JakubSperka/geometeo_logger/calibration_sample/etalon_calibration_sample.csv

 | P, hPa | T, °C | RH, %
3.8.2026 8:03:03 | 996.65 | 35.93 | 29.54
3.8.2026 8:04:03 | 996.68 | 35.96 | 29.65
3.8.2026 8:05:03 | 996.66 | 36.00 | 29.68
3.8.2026 8:06:03 | 996.71 | 36.05 | 29.63
3.8.2026 8:07:03 | 996.69 | 36.09 | 29.60
3.8.2026 8:08:03 | 996.72 | 36.15 | 29.39
3.8.2026 8:09:03 | 996.74 | 36.19 | 29.29
3.8.2026 8:10:03 | 996.74 | 36.33 | 29.07
3.8.2026 8:11:03 | 996.75 | 36.48 | 28.80
3.8.2026 8:12:03 | 996.76 | 36.61 | 28.59
3.8.2026 8:13:03 | 996.78 | 36.68 | 28.42
3.8.2026 8:14:03 | 996.76 | 36.77 | 28.29
3.8.2026 8:15:03 | 996.76 | 36.85 | 28.14
3.8.2026 8:16:03 | 996.76 | 36.92 | 28.05
3.8.2026 8:17:03 | 996.75 | 36.97 | 27.94
3.8.2026 8:18:03 | 996.76 | 37.00 | 27.86
3.8.2026 8:19:03 | 996.77 | 37.04 | 27.78
3.8.2026 8:20:03 | 996.77 | 37.06 | 27.74
3.8.2026 8:21:03 | 996.77 | 37.10 | 27.66
3.8.2026 8:22:03 | 996.75 | 37.13 | 27.60
3.8.2026 8:23:03 | 996.75 | 37.17 | 27.57
3.8.2026 8:24:03 | 996.76 | 37.19 | 27.51
3.8.2026 8:25:03 | 996.76 | 37.23 | 27.44
3.8.2026 8:26:03 | 996.76 | 37.24 | 27.41
3.8.2026 8:27:03 | 996.72 | 37.27 | 27.37
3.8.2026 8:28:03 | 996.72 | 37.32 | 27.31
3.8.2026 8:29:03 | 996.72 | 37.33 | 27.27
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
