JakubSperka/geometeo_logger/calibration_sample/etalon_validation_sample.csv

 | P, hPa | T, °C | RH, %
3.8.2026 13:13:59 | 995.87 | 36.42 | 28.21
3.8.2026 13:14:59 | 995.86 | 36.42 | 29.03
3.8.2026 13:15:59 | 995.84 | 36.50 | 28.40
3.8.2026 13:16:59 | 995.83 | 36.56 | 28.26
3.8.2026 13:17:59 | 995.81 | 36.56 | 28.51
3.8.2026 13:18:59 | 995.78 | 36.58 | 28.78
3.8.2026 13:19:59 | 995.77 | 36.23 | 28.24
3.8.2026 13:20:59 | 995.77 | 35.81 | 28.59
3.8.2026 13:21:59 | 995.77 | 35.21 | 28.88
3.8.2026 13:22:59 | 995.78 | 34.63 | 29.39
3.8.2026 13:23:59 | 995.77 | 34.02 | 30.06
3.8.2026 13:24:59 | 995.74 | 33.63 | 30.46
3.8.2026 13:25:59 | 995.74 | 33.16 | 30.86
3.8.2026 13:26:59 | 995.72 | 32.77 | 31.19
3.8.2026 13:27:59 | 995.71 | 32.50 | 31.57
3.8.2026 13:28:59 | 995.74 | 32.23 | 31.76
3.8.2026 13:29:59 | 995.73 | 31.99 | 31.85
3.8.2026 13:30:59 | 995.73 | 31.78 | 31.99
3.8.2026 13:31:59 | 995.72 | 31.65 | 32.11
3.8.2026 13:32:59 | 995.70 | 31.47 | 32.24
3.8.2026 13:33:59 | 995.67 | 31.28 | 32.26
3.8.2026 13:34:59 | 995.64 | 31.11 | 32.38
3.8.2026 13:35:59 | 995.64 | 31.13 | 32.31
3.8.2026 13:36:59 | 995.62 | 31.00 | 32.33
3.8.2026 13:37:59 | 995.62 | 30.95 | 32.42
3.8.2026 13:38:59 | 995.61 | 30.94 | 32.36
3.8.2026 13:39:59 | 995.59 | 30.90 | 32.43
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
