JakubSperka/geometeo_logger/_stable/geometeo_logger_v0_9_1_stable.ino

#include <Arduino.h>
#include <Wire.h>
#include <SPI.h>
#include <FS.h>
#include <SD.h>
#include <TFT_eSPI.h>

#include "FT6236.h"

#include <Adafruit_SHT4x.h>
#include <Adafruit_BMP280.h>
#include <RTClib.h>
#include <Preferences.h>
#include <WiFi.h>
#include <WebServer.h>
#include <esp_arduino_version.h>
#include <pgmspace.h>

// ============================================================
// GEOMETEO LOGGER - INFORMACIE O FIRMVÉRI
// Pri dalsej verzii staci upravit hodnotu APP_VERSION.
// ============================================================

constexpr char APP_NAME[] = "GEOMETEO LOGGER";
constexpr char APP_VERSION[] = "v0.9.1 (STABLE)";

// ============================================================
// HARDVER: INTERNA I2C ZBERNICA - DOTYK
// ============================================================

constexpr uint8_t INTERNAL_I2C_SDA = 42;
constexpr uint8_t INTERNAL_I2C_SCL = 2;

// ============================================================
// HARDVER: EXTERNA I2C ZBERNICA - METEO SENZOR A RTC
// ============================================================

constexpr uint8_t EXTERNAL_I2C_SDA = 5;
constexpr uint8_t EXTERNAL_I2C_SCL = 6;
constexpr uint32_t I2C_FREQUENCY = 100000;

// ============================================================
// HARDVER: SD KARTA - ESPD-35 v3.2
// ============================================================

constexpr uint8_t SD_SCK_PIN = 14;
constexpr uint8_t SD_MISO_PIN = 21;
constexpr uint8_t SD_MOSI_PIN = 38;
constexpr uint8_t SD_CS_PIN = 17;
constexpr uint32_t SD_SPI_FREQUENCY = 4000000;

// ============================================================
// SENZORY
// ============================================================

constexpr uint8_t BMP280_I2C_ADDRESS = 0x77;

// ============================================================
// BATERIA - ESPD-35 v3.2
// ============================================================

constexpr uint8_t BATTERY_ADC_PIN = 9;
constexpr float BATTERY_DIVIDER_RATIO = 1.7693877551F;
constexpr uint32_t BATTERY_INTERVAL_MS = 5000;
constexpr uint8_t BATTERY_SAMPLE_COUNT = 16;

constexpr uint8_t BATTERY_WARNING_PERCENT = 25;
constexpr uint8_t BATTERY_CRITICAL_PERCENT = 10;

// ============================================================
// SPOĽAHLIVOST A VALIDACIA
// ============================================================

constexpr uint32_t SD_RECOVERY_INTERVAL_MS = 5000;
constexpr uint8_t SD_WRITE_ATTEMPTS = 2;

// Ochrana FAT32 a volneho miesta.
// Jeden FAT32 subor moze mat najviac 4 GiB - 1 B. Relacia sa
// preventivne rozdeli uz pri 3800 MiB, aby zostala bezpecna rezerva.
constexpr uint64_t FAT32_MAX_FILE_SIZE_BYTES = 0xFFFFFFFFULL;

// Pre overenie delenia bez vytvarania viacgigabajtoveho suboru
// mozno docasne nastavit STORAGE_ROTATION_TEST_MODE na true.
// V produkcnej verzii musi zostat false.
constexpr bool STORAGE_ROTATION_TEST_MODE = false;

constexpr uint64_t SESSION_FILE_ROTATE_LIMIT_BYTES =
    STORAGE_ROTATION_TEST_MODE
        ? 64ULL * 1024ULL
        : 3800ULL * 1024ULL * 1024ULL;

constexpr uint64_t SD_LOW_SPACE_WARNING_BYTES =
    32ULL * 1024ULL * 1024ULL;

constexpr uint64_t SD_NORMAL_FREE_RESERVE_BYTES =
    4ULL * 1024ULL * 1024ULL;

constexpr uint64_t SD_EMERGENCY_FREE_RESERVE_BYTES =
    64ULL * 1024ULL;

constexpr uint32_t SD_SPACE_CHECK_INTERVAL_MS = 5000;
constexpr size_t SESSION_FILE_PATH_LENGTH = 112;
constexpr size_t SESSION_MAX_FILE_PARTS = 32;
constexpr size_t CSV_RECORD_ESTIMATE_BYTES = 1024;

static_assert(
    SESSION_FILE_ROTATE_LIMIT_BYTES <
        FAT32_MAX_FILE_SIZE_BYTES,
    "Limit rotacie musi byt mensi ako limit FAT32."
);

constexpr float MIN_VALID_TEMPERATURE_C = -40.0F;
constexpr float MAX_VALID_TEMPERATURE_C = 85.0F;
constexpr float MIN_VALID_HUMIDITY_PERCENT = 0.0F;
constexpr float MAX_VALID_HUMIDITY_PERCENT = 100.0F;
constexpr float MIN_VALID_PRESSURE_HPA = 300.0F;
constexpr float MAX_VALID_PRESSURE_HPA = 1100.0F;

constexpr uint16_t MIN_VALID_RTC_YEAR = 2020;
constexpr uint16_t MAX_VALID_RTC_YEAR = 2099;

// ============================================================
// KALIBRACIA - LINEARNA KOREKCIA y = a*x + b
// Neutralne hodnoty nemenia meranie. Konkretne koeficienty
// sa doplnia po porovnani s laboratornym meradlom.
// ============================================================

constexpr float DEFAULT_CALIBRATION_SCALE = 1.0F;
constexpr float DEFAULT_CALIBRATION_OFFSET = 0.0F;

constexpr float MIN_CALIBRATION_SCALE = 0.5F;
constexpr float MAX_CALIBRATION_SCALE = 1.5F;

constexpr float MIN_TEMPERATURE_OFFSET_C = -20.0F;
constexpr float MAX_TEMPERATURE_OFFSET_C = 20.0F;
constexpr float MIN_HUMIDITY_OFFSET_PERCENT = -50.0F;
constexpr float MAX_HUMIDITY_OFFSET_PERCENT = 50.0F;
constexpr float MIN_PRESSURE_OFFSET_HPA = -150.0F;
constexpr float MAX_PRESSURE_OFFSET_HPA = 150.0F;

// ============================================================
// CASOVANIE
// ============================================================

constexpr uint32_t SENSOR_INTERVAL_MS = 1000;
constexpr uint32_t SAVE_FEEDBACK_MS = 1300;
constexpr uint32_t MESSAGE_DURATION_MS = 2500;

constexpr uint16_t DEFAULT_AUTO_LOG_INTERVAL_SECONDS = 5;
constexpr uint8_t DEFAULT_BRIGHTNESS_PERCENT = 100;

constexpr uint16_t AUTO_LOG_INTERVAL_OPTIONS_SECONDS[] = {
    1,
    5,
    10,
    30,
    60
};

constexpr uint8_t MIN_BRIGHTNESS_PERCENT = 10;
constexpr uint8_t MAX_BRIGHTNESS_PERCENT = 100;

// ============================================================
// USPORA ENERGIE DISPLEJA
// Po nastavenej necinnosti sa displej stlmi na 5 %.
// Po dalsich 30 sekundach sa podsvietenie vypne.
// Senzory, RTC a zapis na SD pokracuju bez prerusenia.
// ============================================================

constexpr bool DEFAULT_POWER_SAVING_ENABLED = true;
constexpr uint16_t DEFAULT_POWER_DIM_TIMEOUT_SECONDS = 60;

constexpr uint16_t POWER_DIM_TIMEOUT_OPTIONS_SECONDS[] = {
    30,
    60,
    120,
    300
};

constexpr size_t POWER_DIM_TIMEOUT_OPTION_COUNT =
    sizeof(POWER_DIM_TIMEOUT_OPTIONS_SECONDS) /
    sizeof(POWER_DIM_TIMEOUT_OPTIONS_SECONDS[0]);

constexpr uint8_t POWER_DIM_BRIGHTNESS_PERCENT = 5;
constexpr uint16_t POWER_OFF_DELAY_SECONDS = 30;

constexpr size_t AUTO_LOG_INTERVAL_OPTION_COUNT =
    sizeof(AUTO_LOG_INTERVAL_OPTIONS_SECONDS) /
    sizeof(AUTO_LOG_INTERVAL_OPTIONS_SECONDS[0]);

constexpr uint32_t BACKLIGHT_PWM_FREQUENCY = 5000;
constexpr uint8_t BACKLIGHT_PWM_RESOLUTION = 8;
constexpr uint8_t BACKLIGHT_PWM_CHANNEL = 0;

// ============================================================
// RELACIE A IDENTIFIKATORY
// ============================================================

constexpr size_t IDENTIFIER_MAX_LENGTH = 16;

constexpr char SESSION_DIRECTORY[] = "/sessions";

constexpr char SESSION_CSV_HEADER[] =
    "session_id,timestamp,record_type,station,target_point,"
    "temperature_c,humidity_pct,pressure_hpa,"
    "battery_voltage_v,battery_percent,"
    "temperature_raw_c,humidity_raw_pct,pressure_raw_hpa,"
    "calibration_enabled,temperature_scale,temperature_offset_c,"
    "humidity_scale,humidity_offset_pct,"
    "pressure_scale,pressure_offset_hpa";

// ============================================================
// WI-FI EXPORT UKONCENYCH RELACII
// ============================================================

// Zariadenie vytvori vlastny pristupovy bod. Internet ani router
// nie su potrebne. Ukoncene CSV relacie sa stahuju cez prehliadac.
constexpr char WIFI_EXPORT_PASSWORD[] = "geometeo";
constexpr uint16_t WIFI_EXPORT_PORT = 80;
constexpr uint32_t WIFI_EXPORT_IDLE_TIMEOUT_MS = 5UL * 60UL * 1000UL;
constexpr uint32_t WIFI_EXPORT_UI_REFRESH_MS = 1000;
constexpr uint8_t WIFI_EXPORT_MAX_CLIENTS = 4;

const IPAddress WIFI_EXPORT_IP(192, 168, 4, 1);
const IPAddress WIFI_EXPORT_GATEWAY(192, 168, 4, 1);
const IPAddress WIFI_EXPORT_SUBNET(255, 255, 255, 0);

// ============================================================
// GRAFY RELACIE
// ============================================================

// Na displeji sa vykresli najviac 240 bodov. Pri volbe VSETKY
// sa vacsia relacia priebezne zmensi do priemerovych intervalov.
constexpr size_t GRAPH_LAST_RECORD_COUNT = 120;
constexpr size_t GRAPH_MAX_POINT_COUNT = 240;
constexpr size_t GRAPH_CSV_LINE_LENGTH = 384;

// Suhrn relacie sa prekresli kazdu sekundu.
// Rozsah 120 sa aktualizuje po kazdom uspesnom AUTO zapise.
// Rozsah VSETKY sa pri velkej relacii znovu nacita najviac
// raz za 10 sekund, aby sa zbytocne nezatazovala SD karta.
constexpr uint32_t GRAPH_SUMMARY_REFRESH_INTERVAL_MS = 5000;
constexpr uint32_t GRAPH_ALL_REFRESH_MIN_INTERVAL_MS = 10000;

// ============================================================
// ARCHIV UKONCENYCH RELACII
// ============================================================

// V pamati sa uchovava zoznam najnovsich ukoncenych relacii.
// Pri vacsom pocte suborov zostane dostupnych 96 najnovsich.
constexpr size_t ARCHIVE_MAX_SESSIONS = 96;
constexpr size_t ARCHIVE_PAGE_SIZE = 5;
constexpr size_t ARCHIVE_PATH_LENGTH = SESSION_FILE_PATH_LENGTH;
constexpr size_t ARCHIVE_SESSION_ID_LENGTH = 32;
constexpr size_t ARCHIVE_CSV_LINE_LENGTH = 384;

// ============================================================
// OBJEKTY
// ============================================================

TFT_eSPI tft = TFT_eSPI();

// FT6236 pouziva fyzicke rozmery dotykovej vrstvy.
// Transformaciu do portretnej orientacie vykona setRotation(0).
FT6236 touch = FT6236(480, 320);

Adafruit_SHT4x sht40;
Adafruit_BMP280 bmp280(&Wire1);
RTC_DS3231 rtc;

SPIClass sdSpi(FSPI);
Preferences preferences;
WebServer wifiExportServer(WIFI_EXPORT_PORT);

// ============================================================
// FARBY
// ============================================================

// Cierny zaklad zostava rovnaky; akcent je volitelny v nastaveniach.
constexpr uint16_t COLOR_BACKGROUND = TFT_BLACK;
constexpr uint16_t COLOR_PANEL = 0x18E3;          // tmava antracitova
constexpr uint16_t COLOR_DISABLED = 0x4208;
constexpr uint16_t COLOR_INPUT = 0x28E2;          // tepla ciernosiva

uint16_t COLOR_PANEL_BORDER = 0x5980;
uint16_t COLOR_PRIMARY = 0xFC00;
uint16_t COLOR_ACCENT = 0xFD46;

constexpr uint16_t COLOR_TEXT = TFT_WHITE;
constexpr uint16_t COLOR_SECONDARY_TEXT = 0xD699;  // tepla svetlosiva

constexpr uint16_t COLOR_OK = TFT_GREEN;
uint16_t COLOR_WARNING = COLOR_PRIMARY;
constexpr uint16_t COLOR_ERROR = TFT_RED;

// Stavové bodky na hlavnej obrazovke nepodliehajú farebnej téme.
// Zelená = OK, oranžová = upozornenie/neaktívny stav, červená = chyba.
constexpr uint16_t STATUS_COLOR_OK = 0x07E0;
constexpr uint16_t STATUS_COLOR_WARNING = 0xFD20;
constexpr uint16_t STATUS_COLOR_ERROR = 0xF800;

// ============================================================
// BITMAPA IKONY NASTAVENI - 32 x 32 px
// Zdroj: gear.txt. Nulove bity tvoria samotny symbol ozubenia.
// ============================================================

constexpr uint8_t SETTINGS_GEAR_BITMAP_WIDTH = 32;
constexpr uint8_t SETTINGS_GEAR_BITMAP_HEIGHT = 32;

const uint8_t SETTINGS_GEAR_BITMAP[] PROGMEM = {
    0x00, 0x07, 0xE0, 0x00, 0x00, 0x0F, 0xF0, 0x00, 0x01, 0x0F, 0xF0, 0x00, 0x07, 0x8F, 0xF1, 0xE0,
    0x0F, 0xDF, 0xFB, 0xF0, 0x1F, 0xFF, 0xFF, 0xF8, 0x1F, 0xFF, 0xFF, 0xF8, 0x1F, 0xFF, 0xFF, 0xF8,
    0x0F, 0xFF, 0xFF, 0xF0, 0x07, 0xFF, 0xFF, 0xE0, 0x07, 0xFF, 0xFF, 0xE0, 0x0F, 0xFC, 0x3F, 0xF0,
    0x7F, 0xF8, 0x1F, 0xFF, 0xFF, 0xF0, 0x0F, 0xFF, 0xFF, 0xE0, 0x07, 0xFF, 0xFF, 0xE0, 0x07, 0xFF,
    0xFF, 0xE0, 0x07, 0xFF, 0xFF, 0xF0, 0x0F, 0xFF, 0xFF, 0xF8, 0x1F, 0xFF, 0x0F, 0xFC, 0x3F, 0xF0,
    0x07, 0xFF, 0xFF, 0xE0, 0x07, 0xFF, 0xFF, 0xE0, 0x0F, 0xFF, 0xFF, 0xF0, 0x1F, 0xFF, 0xFF, 0xF8,
    0x1F, 0xFF, 0xFF, 0xF8, 0x1F, 0xFF, 0xFF, 0xF8, 0x0F, 0xFF, 0xFF, 0xF0, 0x07, 0x8F, 0xF1, 0xE0,
    0x00, 0x0F, 0xF0, 0x00, 0x00, 0x0F, 0xF0, 0x00, 0x00, 0x07, 0xE0, 0x00, 0x00, 0x07, 0xE0, 0x00,
};


// ============================================================
// BITMAPA IKONY WI-FI EXPORTU - 32 x 32 px
// Zdroj: wifi(1).txt.
// ============================================================

constexpr uint8_t WIFI_BITMAP_WIDTH = 32;
constexpr uint8_t WIFI_BITMAP_HEIGHT = 32;

const uint8_t WIFI_BITMAP[] PROGMEM = {
    0x00, 0x00, 0x00, 0x00, 0x00, 0x00, 0x00, 0x00, 0x00, 0x3F, 0xFC, 0x00, 0x01, 0xFF, 0xFF, 0x00,
    0x07, 0xFF, 0xFF, 0xC0, 0x1F, 0xFF, 0xFF, 0xF0, 0x3F, 0xFF, 0xFF, 0xFC, 0x7F, 0xF0, 0x1F, 0xFE,
    0xFF, 0x80, 0x03, 0xFF, 0xFE, 0x1F, 0xF8, 0x7F, 0xFC, 0x7F, 0xFE, 0x3F, 0xF8, 0xFF, 0xFF, 0x9F,
    0x63, 0xFF, 0xFF, 0xEF, 0x07, 0xFF, 0xFF, 0xE0, 0x0F, 0xF8, 0x1F, 0xF0, 0x0F, 0xE0, 0x07, 0xF0,
    0x0F, 0xC3, 0xE1, 0xF0, 0x0F, 0x9F, 0xF8, 0xF0, 0x00, 0x3F, 0xFE, 0x00, 0x00, 0x7F, 0xFE, 0x00,
    0x00, 0x7F, 0xFF, 0x00, 0x00, 0x7E, 0x3F, 0x00, 0x00, 0x78, 0x1E, 0x00, 0x00, 0x03, 0xC0, 0x00,
    0x00, 0x07, 0xE0, 0x00, 0x00, 0x07, 0xE0, 0x00, 0x00, 0x07, 0xE0, 0x00, 0x00, 0x07, 0xE0, 0x00,
    0x00, 0x03, 0xE0, 0x00, 0x00, 0x01, 0xC0, 0x00, 0x00, 0x00, 0x00, 0x00, 0x00, 0x00, 0x00, 0x00
};


// ============================================================
// BITMAPA IKONY GRAFOV - 32 x 32 px
// Zdroj: graph.txt.
// ============================================================

constexpr uint8_t GRAPH_BITMAP_WIDTH = 32;
constexpr uint8_t GRAPH_BITMAP_HEIGHT = 32;

const uint8_t GRAPH_BITMAP[] PROGMEM = {
    0x20, 0x00, 0x00, 0x00, 0x78, 0x00, 0x00, 0x0E, 0xF8, 0x00, 0x00, 0x1E, 0xF8, 0x00, 0x00, 0x1E,
    0xF8, 0x00, 0x00, 0x3E, 0xF8, 0x00, 0x00, 0x3E, 0xF8, 0x00, 0x00, 0x3C, 0xF8, 0x00, 0x0E, 0x78,
    0xF8, 0x00, 0x0F, 0xF8, 0xF8, 0x00, 0x1F, 0xF0, 0xF8, 0x00, 0x3F, 0xF0, 0xF8, 0x00, 0x3F, 0xE0,
    0xF8, 0x00, 0x7F, 0xE0, 0xF8, 0x1C, 0xF3, 0xC0, 0xF8, 0x3F, 0xF1, 0x80, 0xF8, 0x7F, 0xE0, 0x00,
    0xF8, 0xFF, 0xE0, 0x00, 0xF8, 0xFF, 0xC0, 0x00, 0xF9, 0xF3, 0xC0, 0x00, 0xF9, 0xE0, 0x00, 0x00,
    0xFB, 0xE0, 0x00, 0x00, 0xFB, 0xC0, 0x00, 0x00, 0xFF, 0x80, 0x00, 0x00, 0xFF, 0x80, 0x00, 0x00,
    0xFF, 0x00, 0x00, 0x00, 0xFE, 0x00, 0x00, 0x00, 0xFC, 0x00, 0x00, 0x00, 0xFF, 0xFF, 0xFF, 0xFE,
    0xFF, 0xFF, 0xFF, 0xFF, 0xFF, 0xFF, 0xFF, 0xFF, 0xFF, 0xFF, 0xFF, 0xFF, 0x7F, 0xFF, 0xFF, 0xFE
};


// ============================================================
// BITMAPA IKONY ARCHIVU RELACII - 32 x 32 px
// Zdroj: save.txt.
// ============================================================

constexpr uint8_t ARCHIVE_BITMAP_WIDTH = 32;
constexpr uint8_t ARCHIVE_BITMAP_HEIGHT = 32;

const uint8_t ARCHIVE_BITMAP[] PROGMEM = {
    0x3F, 0xFF, 0xF8, 0x00, 0x3F, 0xFF, 0xFC, 0x00, 0x3F, 0xFF, 0xFE, 0x00, 0x3F, 0xFF, 0xFF, 0x00,
  0x3F, 0xFF, 0xFF, 0x80, 0x3C, 0xF8, 0x1F, 0xC0, 0x3C, 0xF8, 0x1F, 0xE0, 0x3C, 0xF8, 0x1F, 0xF8,
  0x3C, 0xFF, 0xFF, 0xFC, 0x3C, 0xFF, 0xFF, 0xFC, 0x3C, 0xFF, 0xFF, 0x7C, 0x3C, 0xFF, 0xFF, 0x3C,
  0x3C, 0x00, 0x00, 0x3C, 0x3C, 0x00, 0x00, 0x3C, 0x3C, 0x00, 0x00, 0x3C, 0x3C, 0x00, 0x00, 0x3C,
  0x3C, 0x00, 0x00, 0x3C, 0x3C, 0x00, 0x00, 0x3C, 0x3C, 0xFF, 0xFF, 0x3C, 0x3C, 0xFF, 0xFF, 0x3C,
  0x3C, 0xFF, 0xFF, 0x3C, 0x3C, 0xFF, 0xFF, 0x3C, 0x3C, 0xF8, 0x1F, 0x3C, 0x3C, 0xF8, 0x1F, 0x3C,
  0x3C, 0xF8, 0x1F, 0x3C, 0x3C, 0xF8, 0x1F, 0x3C, 0x3C, 0xF8, 0x1F, 0x3C, 0x3F, 0xFF, 0xFF, 0xFC,
  0x3F, 0xFF, 0xFF, 0xFC, 0x3F, 0xFF, 0xFF, 0xFC, 0x3F, 0xFF, 0xFF, 0xFC, 0x3F, 0xFF, 0xFF, 0xFC
};


// ============================================================
// DATOVE TYPY
// ============================================================

struct Measurement
{
    DateTime timestamp;

    // Hodnoty pouzivane na displeji, v grafoch a v hlavnych
    // CSV stlpcoch. Pri zapnutej kalibracii su korigovane.
    float temperatureC;
    float humidityPercent;
    float pressureHpa;

    // Povodne hodnoty priamo zo senzorov. Ukladaju sa do CSV,
    // aby bolo mozne kalibraciu neskor spatne skontrolovat.
    float rawTemperatureC;
    float rawHumidityPercent;
    float rawPressureHpa;

    bool valid;
};

struct CalibrationConfig
{
    bool enabled;
    float temperatureScale;
    float temperatureOffsetC;
    float humidityScale;
    float humidityOffsetPercent;
    float pressureScale;
    float pressureOffsetHpa;
};

enum class CalibrationParameter : uint8_t
{
    Temperature,
    Humidity,
    Pressure
};

enum class CalibrationEditField : uint8_t
{
    None,
    Scale,
    Offset
};

enum class AccentTheme : uint8_t
{
    Orange = 0,
    Blue,
    Green,
    Red,
    Purple,
    Gray,
    Yellow,
    Lime,
    Cream,
    Pink
};

struct AccentPalette
{
    uint16_t primary;
    uint16_t accent;
    uint16_t panelBorder;
    const char *name;
    const char *webPrimary;
    const char *webBorder;
};

constexpr AccentPalette ACCENT_PALETTES[] = {
    {
        0xFC00,
        0xFD46,
        0x5980,
        "ORANZOVA",
        "#ff8a00",
        "#6b4317"
    },
    {
        0x453E,
        0x965F,
        0x1AD0,
        "MODRA",
        "#42a5f5",
        "#1e5a86"
    },
    {
        0x65CD,
        0xA6B4,
        0x2B47,
        "ZELENA",
        "#66bb6a",
        "#2d6b3a"
    },
    {
        0xEA8A,
        0xECD3,
        0x8965,
        "CERVENA",
        "#ef5350",
        "#8a2e2b"
    },
    {
        0xAA37,
        0xCC9B,
        0x614E,
        "FIALOVA",
        "#ab47bc",
        "#672a72"
    },
    {
        0x9CF3,
        0xD69A,
        0x5AEB,
        "SEDA",
        "#9e9e9e",
        "#5e5e5e"
    },
    {
        0xFEC6,
        0xFF8E,
        0x8BA2,
        "ZLTA",
        "#fdd835",
        "#8a7715"
    },
    {
        0xB709,
        0xD7AF,
        0x5BA3,
        "LIMETKOVA",
        "#b7e04a",
        "#58751f"
    },
    {
        0xF738,
        0xFFBA,
        0x8BAA,
        "KREMOVA",
        "#f3e5c0",
        "#8a7650"
    },
    {
        0xEAD2,
        0xF538,
        0x898B,
        "RUZOVA",
        "#ec5a90",
        "#8a3158"
    }
};

constexpr size_t ACCENT_THEME_COUNT =
    sizeof(ACCENT_PALETTES) /
    sizeof(ACCENT_PALETTES[0]);

enum class Screen : uint8_t
{
    Main,
    Keyboard,
    ConfirmEndSession,
    Settings,
    DateTimeEditor,
    Recovery,
    Graphs,
    ArchiveList,
    ArchiveDetail,
    Calibration,
    CalibrationEditor,
    PowerSettings,
    ThemeSettings,
    WifiExport
};

enum class DisplayPowerState : uint8_t
{
    Awake,
    Dimmed,
    Off
};

enum class EditField : uint8_t
{
    None,
    Station,
    TargetPoint
};

enum class KeyboardMode : uint8_t
{
    Numeric,
    Alphabetic
};

enum class SaveButtonState : uint8_t
{
    Idle,
    Success,
    Error
};

enum class StatusState : uint8_t
{
    Ok,
    Warning,
    Error
};

enum class MeasurementError : uint8_t
{
    None,
    DevicesNotReady,
    RtcInvalid,
    ShtReadFailed,
    PressureReadFailed,
    TemperatureOutOfRange,
    HumidityOutOfRange,
    PressureOutOfRange
};


enum class GraphRange : uint8_t
{
    Last120,
    All
};

enum class GraphParameter : uint8_t
{
    Temperature,
    Humidity,
    Pressure
};

struct GraphSample
{
    uint32_t unixTime;
    float temperatureC;
    float humidityPercent;
    float pressureHpa;
};

struct GraphStatistics
{
    float minimum;
    float maximum;
    double sum;
    uint32_t count;
};

struct ArchiveSession
{
    char filePath[ARCHIVE_PATH_LENGTH];
    char sessionId[ARCHIVE_SESSION_ID_LENGTH];
    char station[IDENTIFIER_MAX_LENGTH + 1];
    uint32_t startUnix;
    uint32_t endUnix;
    uint64_t fileSize;
    uint16_t partCount;
};

struct ArchiveSessionDetailData
{
    bool loaded;
    char filePath[ARCHIVE_PATH_LENGTH];
    char sessionId[ARCHIVE_SESSION_ID_LENGTH];
    char station[IDENTIFIER_MAX_LENGTH + 1];
    uint32_t startUnix;
    uint32_t endUnix;
    uint32_t autoRecordCount;
    uint32_t manualRecordCount;
    uint16_t partCount;
    uint64_t totalFileSize;
    GraphStatistics temperatureStats;
    GraphStatistics humidityStats;
    GraphStatistics pressureStats;
};

struct Rect
{
    int16_t x;
    int16_t y;
    int16_t width;
    int16_t height;

    bool contains(int16_t pointX, int16_t pointY) const
    {
        return
            pointX >= x &&
            pointX < x + width &&
            pointY >= y &&
            pointY < y + height;
    }
};

// ============================================================
// ROZMERY HLAVNEJ OBRAZOVKY - PORTRET 320 x 480
// ============================================================

constexpr Rect STATION_FIELD_RECT{10, 202, 300, 40};
constexpr Rect TARGET_FIELD_RECT{10, 248, 300, 40};

constexpr Rect SESSION_TOGGLE_BUTTON_RECT{10, 294, 300, 42};

constexpr Rect SAVE_BUTTON_RECT{10, 342, 300, 54};

constexpr Rect CONFIRM_BACK_BUTTON_RECT{10, 410, 145, 52};
constexpr Rect CONFIRM_END_BUTTON_RECT{165, 410, 145, 52};

constexpr uint8_t MAIN_SHORTCUT_ICON_SIZE = 36;

constexpr Rect WIFI_SHORTCUT_RECT{160, 440, 40, 40};
constexpr Rect ARCHIVE_SHORTCUT_RECT{200, 440, 40, 40};
constexpr Rect GRAPH_SHORTCUT_RECT{240, 440, 40, 40};
constexpr Rect SETTINGS_SHORTCUT_RECT{280, 440, 40, 40};

constexpr Rect STATUS_MESSAGE_RECT{0, 440, 158, 40};

// ============================================================
// WI-FI EXPORT
// ============================================================

constexpr Rect WIFI_STATUS_PANEL_RECT{10, 52, 300, 224};
constexpr Rect WIFI_ACTION_RECT{10, 292, 300, 58};
constexpr Rect WIFI_REFRESH_RECT{10, 364, 145, 44};
constexpr Rect WIFI_BACK_RECT{10, 420, 300, 44};

// ============================================================
// ARCHIV UKONCENYCH RELACII
// ============================================================

constexpr Rect ARCHIVE_ROW_RECTS[ARCHIVE_PAGE_SIZE] = {
    {10, 50, 300, 58},
    {10, 116, 300, 58},
    {10, 182, 300, 58},
    {10, 248, 300, 58},
    {10, 314, 300, 58}
};

constexpr Rect ARCHIVE_BACK_RECT{10, 414, 72, 50};
constexpr Rect ARCHIVE_PREVIOUS_RECT{90, 414, 64, 50};
constexpr Rect ARCHIVE_NEXT_RECT{162, 414, 64, 50};
constexpr Rect ARCHIVE_REFRESH_RECT{234, 414, 76, 50};

constexpr Rect ARCHIVE_DETAIL_PANEL_RECT{10, 50, 300, 350};
constexpr Rect ARCHIVE_DETAIL_BACK_RECT{10, 414, 145, 50};
constexpr Rect ARCHIVE_DETAIL_GRAPH_RECT{165, 414, 145, 50};

// ============================================================
// OBRAZOVKA GRAFOV A SUHRNU RELACIE
// ============================================================

constexpr Rect GRAPH_TEMPERATURE_RECT{10, 48, 94, 40};
constexpr Rect GRAPH_HUMIDITY_RECT{113, 48, 94, 40};
constexpr Rect GRAPH_PRESSURE_RECT{216, 48, 94, 40};

constexpr Rect GRAPH_SUMMARY_RECT{10, 96, 300, 58};
constexpr Rect GRAPH_PANEL_RECT{10, 162, 300, 238};

constexpr Rect GRAPH_BACK_RECT{10, 414, 80, 50};
constexpr Rect GRAPH_LAST120_RECT{98, 414, 104, 50};
constexpr Rect GRAPH_ALL_RECT{210, 414, 100, 50};

// ============================================================
// OBRAZOVKA OBNOVY NEDOKONCENEJ RELACIE
// ============================================================

constexpr Rect RECOVERY_CONTINUE_RECT{10, 300, 300, 50};
constexpr Rect RECOVERY_END_RECT{10, 360, 145, 50};
constexpr Rect RECOVERY_NEW_RECT{165, 360, 145, 50};

// ============================================================
// ROZMERY OBRAZOVKY NASTAVENI
// ============================================================

constexpr Rect SETTINGS_DATETIME_PANEL_RECT{10, 54, 300, 82};
constexpr Rect SETTINGS_DATETIME_BUTTON_RECT{20, 92, 280, 34};

constexpr Rect SETTINGS_INTERVAL_BUTTON_RECTS[] = {
    {10, 178, 54, 48},
    {70, 178, 54, 48},
    {130, 178, 54, 48},
    {190, 178, 54, 48},
    {250, 178, 60, 48}
};

constexpr Rect SETTINGS_BRIGHTNESS_TOUCH_RECT{20, 270, 280, 64};
constexpr Rect SETTINGS_BRIGHTNESS_TRACK_RECT{28, 294, 264, 12};

constexpr Rect SETTINGS_THEME_RECT{242, 5, 68, 34};

constexpr Rect SETTINGS_CALIBRATION_RECT{10, 354, 145, 44};
constexpr Rect SETTINGS_POWER_RECT{165, 354, 145, 44};
constexpr Rect SETTINGS_BACK_RECT{10, 410, 145, 54};
constexpr Rect SETTINGS_GENERAL_SAVE_RECT{165, 410, 145, 54};

// ============================================================
// ROZMERY VYBERU FAREBNEJ SCHEMY
// ============================================================

constexpr Rect THEME_OPTION_RECTS[ACCENT_THEME_COUNT] = {
    {10, 58, 145, 56},
    {165, 58, 145, 56},

    {10, 122, 145, 56},
    {165, 122, 145, 56},

    {10, 186, 145, 56},
    {165, 186, 145, 56},

    {10, 250, 145, 56},
    {165, 250, 145, 56},

    {10, 314, 145, 56},
    {165, 314, 145, 56}
};

constexpr Rect THEME_BACK_RECT{10, 414, 145, 50};
constexpr Rect THEME_SAVE_RECT{165, 414, 145, 50};

// ============================================================
// ROZMERY USPORY ENERGIE
// ============================================================

constexpr Rect POWER_ENABLED_RECT{10, 58, 300, 54};

constexpr Rect POWER_TIMEOUT_RECTS[
    POWER_DIM_TIMEOUT_OPTION_COUNT
] = {
    {10, 166, 67, 52},
    {87, 166, 67, 52},
    {164, 166, 67, 52},
    {241, 166, 69, 52}
};

constexpr Rect POWER_INFO_RECT{10, 238, 300, 156};
constexpr Rect POWER_BACK_RECT{10, 414, 145, 50};
constexpr Rect POWER_SAVE_RECT{165, 414, 145, 50};

// ============================================================
// ROZMERY KALIBRACIE
// ============================================================

constexpr Rect CALIBRATION_TEMPERATURE_RECT{10, 50, 94, 40};
constexpr Rect CALIBRATION_HUMIDITY_RECT{113, 50, 94, 40};
constexpr Rect CALIBRATION_PRESSURE_RECT{216, 50, 94, 40};

constexpr Rect CALIBRATION_LIVE_RECT{10, 98, 300, 88};
constexpr Rect CALIBRATION_SCALE_RECT{10, 196, 300, 48};
constexpr Rect CALIBRATION_OFFSET_RECT{10, 252, 300, 48};
constexpr Rect CALIBRATION_ENABLED_RECT{10, 308, 300, 44};
constexpr Rect CALIBRATION_INFO_RECT{10, 360, 300, 38};
constexpr Rect CALIBRATION_BACK_RECT{10, 414, 145, 50};
constexpr Rect CALIBRATION_SAVE_RECT{165, 414, 145, 50};

constexpr Rect CALIBRATION_EDITOR_DISPLAY_RECT{10, 52, 240, 54};
constexpr Rect CALIBRATION_EDITOR_BACKSPACE_RECT{260, 52, 50, 54};
constexpr Rect CALIBRATION_EDITOR_CLEAR_RECT{10, 114, 300, 28};
constexpr Rect CALIBRATION_EDITOR_BACK_RECT{10, 414, 145, 50};
constexpr Rect CALIBRATION_EDITOR_SAVE_RECT{165, 414, 145, 50};

// ============================================================
// ROZMERY EDITORA DATUMU A CASU
// ============================================================

constexpr Rect DATETIME_DISPLAY_RECT{10, 50, 300, 76};

constexpr Rect DATETIME_BACK_RECT{10, 414, 145, 52};
constexpr Rect DATETIME_SAVE_RECT{165, 414, 145, 52};

// ============================================================
// ROZMERY KLAVESNICE
// ============================================================

constexpr Rect KEYBOARD_INPUT_RECT{10, 48, 244, 48};
constexpr Rect KEYBOARD_BACKSPACE_RECT{262, 48, 48, 48};

constexpr Rect KEYBOARD_MODE_RECT{10, 426, 80, 46};
constexpr Rect KEYBOARD_CANCEL_RECT{98, 426, 104, 46};
constexpr Rect KEYBOARD_OK_RECT{210, 426, 100, 46};

// ============================================================
// STAV ZARIADENI
// ============================================================

bool internalWireReady = false;
bool externalWireReady = false;

bool touchReady = false;
bool sht40Ready = false;
bool bmp280Ready = false;
bool rtcReady = false;
bool sdReady = false;
bool sdSpiStarted = false;
bool batteryAvailable = false;

bool sessionActive = false;
bool pendingSessionRecovery = false;
bool lastAutoWriteOk = false;
bool lastManualWriteOk = false;
bool touchWasPressed = false;

// ============================================================
// STAV APLIKACIE
// ============================================================

Screen currentScreen = Screen::Main;
EditField editedField = EditField::None;
KeyboardMode keyboardMode = KeyboardMode::Numeric;
SaveButtonState saveButtonState = SaveButtonState::Idle;

Measurement currentMeasurement{
    DateTime(2000, 1, 1, 0, 0, 0),
    NAN,
    NAN,
    NAN,
    NAN,
    NAN,
    NAN,
    false
};

Measurement readMeasurement();

// Explicit declarations for helpers used before their implementation.
bool hasCsvExtension(const char *fileName);

uint16_t sessionPartIndexFromPath(
    const char *path
);

void deriveSessionBaseFilePath(
    const char *currentPath,
    char *basePath,
    size_t basePathSize
);

size_t collectSessionPartPaths(
    const char *wantedSessionId,
    char paths[][SESSION_FILE_PATH_LENGTH],
    uint16_t partIndices[],
    size_t maximumParts
);

char station[IDENTIFIER_MAX_LENGTH + 1] = "";
char targetPoint[IDENTIFIER_MAX_LENGTH + 1] = "";
char editBuffer[IDENTIFIER_MAX_LENGTH + 1] = "";

char sessionId[32] = "";
char sessionBaseFilePath[SESSION_FILE_PATH_LENGTH] = "";
char sessionFilePath[SESSION_FILE_PATH_LENGTH] = "";
uint16_t sessionFilePartIndex = 1;

char recoveredStation[IDENTIFIER_MAX_LENGTH + 1] = "";
char recoveredTargetPoint[IDENTIFIER_MAX_LENGTH + 1] = "";
char recoveredSessionId[32] = "";
char recoveredSessionBaseFilePath[SESSION_FILE_PATH_LENGTH] = "";
char recoveredSessionFilePath[SESSION_FILE_PATH_LENGTH] = "";
uint16_t recoveredSessionFilePartIndex = 1;
uint32_t recoveredManualRecordCount = 0;

char statusMessage[64] = "";
uint16_t statusMessageColor = COLOR_SECONDARY_TEXT;

uint32_t lastSensorMillis = 0;
uint32_t lastAutoLogMillis = 0;
uint32_t lastBatteryMillis = 0;
uint32_t lastSdRecoveryAttemptMillis = 0;
uint32_t lastSdSpaceCheckMillis = 0;
uint32_t saveFeedbackUntil = 0;

uint64_t sdTotalBytes = 0;
uint64_t sdUsedBytes = 0;
uint64_t sdFreeBytes = 0;
bool sdSpaceInfoValid = false;
bool sdSpaceLow = false;
bool sdSpaceCritical = false;
bool sdWriteBlockedBySpace = false;
uint32_t statusMessageUntil = 0;
uint32_t manualRecordCount = 0;

float batteryVoltage = NAN;
uint8_t batteryPercent = 0;
uint8_t lastBatteryWarningLevel = 0;

MeasurementError lastMeasurementError =
    MeasurementError::None;

uint16_t autoLogIntervalSeconds =
    DEFAULT_AUTO_LOG_INTERVAL_SECONDS;

uint8_t brightnessPercent =
    DEFAULT_BRIGHTNESS_PERCENT;

uint16_t pendingAutoLogIntervalSeconds =
    DEFAULT_AUTO_LOG_INTERVAL_SECONDS;

uint8_t pendingBrightnessPercent =
    DEFAULT_BRIGHTNESS_PERCENT;

AccentTheme accentTheme =
    AccentTheme::Orange;

AccentTheme pendingAccentTheme =
    AccentTheme::Orange;

bool displayPwmReady = false;
bool brightnessSliderDragging = false;

// Uspora energie displeja.
bool powerSavingEnabled =
    DEFAULT_POWER_SAVING_ENABLED;

uint16_t powerDimTimeoutSeconds =
    DEFAULT_POWER_DIM_TIMEOUT_SECONDS;

bool pendingPowerSavingEnabled =
    DEFAULT_POWER_SAVING_ENABLED;

uint16_t pendingPowerDimTimeoutSeconds =
    DEFAULT_POWER_DIM_TIMEOUT_SECONDS;

DisplayPowerState displayPowerState =
    DisplayPowerState::Awake;

uint32_t lastUserActivityMillis = 0;

// Wi-Fi export je standardne vypnuty a aktivuje sa iba manualne.
bool wifiExportRunning = false;
bool wifiExportRoutesConfigured = false;
char wifiExportSsid[32] = "GeoMeteo";
uint32_t wifiExportStartedMillis = 0;
uint32_t wifiExportLastActivityMillis = 0;
uint32_t wifiExportLastUiRefreshMillis = 0;
uint8_t wifiExportLastClientCount = 0;
char wifiExportStatusMessage[64] = "";

CalibrationConfig calibration{
    false,
    DEFAULT_CALIBRATION_SCALE,
    DEFAULT_CALIBRATION_OFFSET,
    DEFAULT_CALIBRATION_SCALE,
    DEFAULT_CALIBRATION_OFFSET,
    DEFAULT_CALIBRATION_SCALE,
    DEFAULT_CALIBRATION_OFFSET
};

CalibrationConfig pendingCalibration = calibration;
CalibrationParameter calibrationParameter =
    CalibrationParameter::Temperature;
CalibrationEditField calibrationEditField =
    CalibrationEditField::None;

char calibrationEditBuffer[20] = "";
char calibrationEditorError[48] = "";

// 14 cislic: DDMMYYYYHHMMSS
char dateTimeDigits[15] = "";


// ============================================================
// STAV GRAFOV
// ============================================================

GraphRange graphRange = GraphRange::Last120;
GraphParameter graphParameter = GraphParameter::Temperature;

GraphSample graphSamples[GRAPH_MAX_POINT_COUNT];
GraphSample graphRecentBuffer[GRAPH_LAST_RECORD_COUNT];

size_t graphPointCount = 0;
uint32_t graphTotalAutoRecords = 0;
uint32_t graphTotalManualRecords = 0;
uint32_t graphSessionStartUnix = 0;
uint32_t graphSessionLastUnix = 0;

GraphStatistics graphDisplayTemperatureStats;
GraphStatistics graphDisplayHumidityStats;
GraphStatistics graphDisplayPressureStats;

GraphStatistics graphTotalTemperatureStats;
GraphStatistics graphTotalHumidityStats;
GraphStatistics graphTotalPressureStats;

bool graphDataReady = false;
char graphErrorMessage[48] = "";

uint32_t lastGraphSummaryRefreshMillis = 0;
uint32_t lastGraphDataRefreshMillis = 0;
bool graphFullRangeRefreshPending = false;

// Explicitna deklaracia, pretoze funkcia sa pouziva skor,
// nez je v subore uvedena jej implementacia.
void drawGraphSummary(bool redrawPanel);

// Pri zobrazeni archivovanej relacie grafy citaju iny CSV subor
// a neprebieha ziadna ziva aktualizacia.
bool graphViewingArchive = false;

// ============================================================
// STAV ARCHIVU RELACII
// ============================================================

ArchiveSession archiveSessions[ARCHIVE_MAX_SESSIONS];
size_t archiveSessionCount = 0;
size_t archiveCurrentPage = 0;
int16_t selectedArchiveSessionIndex = -1;

ArchiveSessionDetailData archiveDetailData{};

// Zdielany buffer pre zoznam casti jednej relacie.
// Funkcie bezia sekvencne v hlavnej slucke, preto sa buffer
// moze opakovane pouzit bez zatazenia zasobnika.
char sharedSessionPartPaths[
    SESSION_MAX_FILE_PARTS
][SESSION_FILE_PATH_LENGTH];

char archiveStatusMessage[64] = "";

// ============================================================
// CACHE PRE CIASTOCNE PREKRESLOVANIE GUI
// ============================================================

bool mainDateTimeCacheValid = false;
bool mainMeasurementCacheValid = false;
bool mainStatusCacheValid = false;
bool mainMessageCacheValid = false;
bool mainSaveButtonCacheValid = false;

char cachedMainDate[16] = "";
char cachedMainTime[16] = "";
char cachedMainBattery[20] = "";
uint16_t cachedMainBatteryColor = 0;

char cachedTemperatureValue[24] = "";
char cachedHumidityValue[24] = "";
char cachedPressureValue[24] = "";

char cachedMainStatusSignature[64] = "";
char cachedMainMessageSignature[96] = "";

char cachedSaveButtonText[32] = "";
uint16_t cachedSaveFillColor = 0;
uint16_t cachedSaveBorderColor = 0;

// ============================================================
// VSEOBECNE POMOCNE FUNKCIE
// ============================================================

size_t accentThemeIndex(
    AccentTheme theme
)
{
    const size_t index =
        static_cast<size_t>(theme);

    return index < ACCENT_THEME_COUNT
        ? index
        : 0;
}

const AccentPalette &accentPalette(
    AccentTheme theme
)
{
    return ACCENT_PALETTES[
        accentThemeIndex(theme)
    ];
}

void applyAccentTheme(
    AccentTheme theme
)
{
    const AccentPalette &palette =
        accentPalette(theme);

    COLOR_PRIMARY = palette.primary;
    COLOR_ACCENT = palette.accent;
    COLOR_PANEL_BORDER =
        palette.panelBorder;

    // Varovny akcent sleduje zvolenu farebnu schemu.
    COLOR_WARNING = COLOR_PRIMARY;
}

bool sensorsAreReady()
{
    return sht40Ready && bmp280Ready && rtcReady;
}

bool identifierIsEmpty(const char *value)
{
    return value == nullptr || value[0] == '\0';
}

bool manualSaveAvailable()
{
    return
        touchReady &&
        sdReady &&
        !sdSpaceCritical &&
        sessionActive &&
        currentMeasurement.valid &&
        !identifierIsEmpty(station) &&
        !identifierIsEmpty(targetPoint);
}

bool timedEventActive(uint32_t endTime)
{
    if (endTime == 0)
    {
        return false;
    }

    return static_cast<int32_t>(endTime - millis()) > 0;
}

bool saveFeedbackActive()
{
    return
        saveButtonState != SaveButtonState::Idle &&
        timedEventActive(saveFeedbackUntil);
}

void copyIdentifier(
    char *destination,
    size_t destinationSize,
    const char *source
)
{
    if (destinationSize == 0)
    {
        return;
    }

    snprintf(
        destination,
        destinationSize,
        "%s",
        source == nullptr ? "" : source
    );
}

bool identifiersEqual(const char *first, const char *second)
{
    return strcmp(first, second) == 0;
}

void setStatusMessage(
    const char *message,
    uint16_t color = COLOR_SECONDARY_TEXT,
    uint32_t durationMs = MESSAGE_DURATION_MS
)
{
    snprintf(
        statusMessage,
        sizeof(statusMessage),
        "%s",
        message == nullptr ? "" : message
    );

    statusMessageColor = color;

    statusMessageUntil =
        durationMs == 0
            ? 0
            : millis() + durationMs;
}

void clearStatusMessage()
{
    statusMessage[0] = '\0';
    statusMessageUntil = 0;
}

// ============================================================
// CHYBY MERANIA
// ============================================================

const char *measurementErrorText(
    MeasurementError error
)
{
    switch (error)
    {
        case MeasurementError::None:
            return "MERANIE OK";

        case MeasurementError::DevicesNotReady:
            return "SENZORY ALEBO RTC NIE SU PRIPRAVENE";

        case MeasurementError::RtcInvalid:
            return "NEPLATNY DATUM ALEBO CAS RTC";

        case MeasurementError::ShtReadFailed:
            return "CHYBA CITANIA SHT40";

        case MeasurementError::PressureReadFailed:
            return "CHYBA CITANIA BMP280";

        case MeasurementError::TemperatureOutOfRange:
            return "TEPLOTA MIMO PLATNEHO ROZSAHU";

        case MeasurementError::HumidityOutOfRange:
            return "VLHKOST MIMO PLATNEHO ROZSAHU";

        case MeasurementError::PressureOutOfRange:
            return "TLAK MIMO PLATNEHO ROZSAHU";

        default:
            return "NEZNAMA CHYBA MERANIA";
    }
}

bool recordTypeAllowsInvalidMeasurement(
    const char *recordType
)
{
    return
        recordType != nullptr &&
        (
            strncmp(recordType, "SESSION_", 8) == 0 ||
            strncmp(recordType, "FILE_", 5) == 0
        );
}

// ============================================================
// OBNOVA MERACEJ RELACIE V INTERNEJ PAMATI
// ============================================================

void clearPersistentSessionState()
{
    preferences.begin("meteo", false);

    preferences.putBool("sess_act", false);
    preferences.remove("sess_st");
    preferences.remove("sess_tgt");
    preferences.remove("sess_id");
    preferences.remove("sess_base");
    preferences.remove("sess_file");
    preferences.remove("sess_part");
    preferences.remove("sess_man");

    preferences.end();
}

void persistActiveSessionState()
{
    preferences.begin("meteo", false);

    preferences.putBool(
        "sess_act",
        sessionActive
    );

    if (sessionActive)
    {
        preferences.putString(
            "sess_st",
            station
        );

        preferences.putString(
            "sess_tgt",
            targetPoint
        );

        preferences.putString(
            "sess_id",
            sessionId
        );

        preferences.putString(
            "sess_base",
            sessionBaseFilePath
        );

        preferences.putString(
            "sess_file",
            sessionFilePath
        );

        preferences.putUShort(
            "sess_part",
            sessionFilePartIndex
        );

        preferences.putULong(
            "sess_man",
            manualRecordCount
        );
    }
    else
    {
        preferences.remove("sess_st");
        preferences.remove("sess_tgt");
        preferences.remove("sess_id");
        preferences.remove("sess_base");
        preferences.remove("sess_file");
        preferences.remove("sess_part");
        preferences.remove("sess_man");
    }

    preferences.end();
}

bool loadPendingSessionRecovery()
{
    preferences.begin("meteo", true);

    const bool storedActive =
        preferences.getBool(
            "sess_act",
            false
        );

    const String storedStation =
        preferences.getString(
            "sess_st",
            ""
        );

    const String storedTarget =
        preferences.getString(
            "sess_tgt",
            ""
        );

    const String storedSessionId =
        preferences.getString(
            "sess_id",
            ""
        );

    const String storedBaseFilePath =
        preferences.getString(
            "sess_base",
            ""
        );

    const String storedFilePath =
        preferences.getString(
            "sess_file",
            ""
        );

    const uint16_t storedPartIndex =
        preferences.getUShort(
            "sess_part",
            1
        );

    const uint32_t storedManualCount =
        preferences.getULong(
            "sess_man",
            0
        );

    preferences.end();

    if (
        !storedActive ||
        storedStation.length() == 0 ||
        storedSessionId.length() == 0 ||
        storedFilePath.length() == 0
    )
    {
        pendingSessionRecovery = false;
        return false;
    }

    storedStation.toCharArray(
        recoveredStation,
        sizeof(recoveredStation)
    );

    storedTarget.toCharArray(
        recoveredTargetPoint,
        sizeof(recoveredTargetPoint)
    );

    storedSessionId.toCharArray(
        recoveredSessionId,
        sizeof(recoveredSessionId)
    );

    storedFilePath.toCharArray(
        recoveredSessionFilePath,
        sizeof(recoveredSessionFilePath)
    );

    if (storedBaseFilePath.length() > 0)
    {
        storedBaseFilePath.toCharArray(
            recoveredSessionBaseFilePath,
            sizeof(recoveredSessionBaseFilePath)
        );
    }
    else
    {
        deriveSessionBaseFilePath(
            recoveredSessionFilePath,
            recoveredSessionBaseFilePath,
            sizeof(recoveredSessionBaseFilePath)
        );
    }

    const uint16_t detectedPartIndex =
        sessionPartIndexFromPath(
            recoveredSessionFilePath
        );

    recoveredSessionFilePartIndex =
        storedPartIndex > 1
            ? storedPartIndex
            : detectedPartIndex;

    recoveredManualRecordCount =
        storedManualCount;

    pendingSessionRecovery = true;

    Serial.println(
        "NAJDENA NEDOKONCENA RELACIA"
    );

    Serial.printf(
        "STANOVISKO: %s\n",
        recoveredStation
    );

    Serial.printf(
        "SUBOR: %s\n",
        recoveredSessionFilePath
    );

    Serial.printf(
        "MANUALNE ZAZNAMY: %lu\n",
        static_cast<unsigned long>(
            recoveredManualRecordCount
        )
    );

    return true;
}

void resetRuntimeSessionState()
{
    sessionActive = false;
    lastAutoWriteOk = false;
    lastManualWriteOk = false;

    station[0] = '\0';
    targetPoint[0] = '\0';

    sessionId[0] = '\0';
    sessionBaseFilePath[0] = '\0';
    sessionFilePath[0] = '\0';
    sessionFilePartIndex = 1;

    manualRecordCount = 0;
    saveButtonState = SaveButtonState::Idle;
    saveFeedbackUntil = 0;
}

void restoreRecoveredSessionToRuntime()
{
    copyIdentifier(
        station,
        sizeof(station),
        recoveredStation
    );

    copyIdentifier(
        targetPoint,
        sizeof(targetPoint),
        recoveredTargetPoint
    );

    copyIdentifier(
        sessionId,
        sizeof(sessionId),
        recoveredSessionId
    );

    snprintf(
        sessionBaseFilePath,
        sizeof(sessionBaseFilePath),
        "%s",
        recoveredSessionBaseFilePath
    );

    snprintf(
        sessionFilePath,
        sizeof(sessionFilePath),
        "%s",
        recoveredSessionFilePath
    );

    sessionFilePartIndex =
        recoveredSessionFilePartIndex > 0
            ? recoveredSessionFilePartIndex
            : 1;

    manualRecordCount =
        recoveredManualRecordCount;

    sessionActive = true;
    lastAutoWriteOk = false;
    lastManualWriteOk = false;
    lastAutoLogMillis = millis();
}

// ============================================================
// MERANIE BATERIE
// ============================================================

uint8_t batteryPercentFromVoltage(float voltage)
{
    struct CurvePoint
    {
        float voltage;
        uint8_t percent;
    };

    static const CurvePoint CURVE[] = {
        {3.20F, 0},
        {3.50F, 5},
        {3.60F, 10},
        {3.70F, 20},
        {3.75F, 30},
        {3.79F, 40},
        {3.83F, 50},
        {3.87F, 60},
        {3.92F, 70},
        {4.00F, 80},
        {4.10F, 90},
        {4.20F, 100}
    };

    constexpr size_t POINT_COUNT =
        sizeof(CURVE) / sizeof(CURVE[0]);

    if (voltage <= CURVE[0].voltage)
    {
        return CURVE[0].percent;
    }

    if (voltage >= CURVE[POINT_COUNT - 1].voltage)
    {
        return CURVE[POINT_COUNT - 1].percent;
    }

    for (size_t index = 1; index < POINT_COUNT; index++)
    {
        if (voltage <= CURVE[index].voltage)
        {
            const CurvePoint &lower = CURVE[index - 1];
            const CurvePoint &upper = CURVE[index];

            const float fraction =
                (voltage - lower.voltage) /
                (upper.voltage - lower.voltage);

            const float interpolated =
                lower.percent +
                fraction * (upper.percent - lower.percent);

            return static_cast<uint8_t>(
                roundf(interpolated)
            );
        }
    }

    return 0;
}

uint16_t batteryStatusColor()
{
    if (!batteryAvailable)
    {
        return COLOR_DISABLED;
    }

    if (batteryPercent <= BATTERY_CRITICAL_PERCENT)
    {
        return COLOR_ERROR;
    }

    if (batteryPercent <= BATTERY_WARNING_PERCENT)
    {
        return COLOR_WARNING;
    }

    return COLOR_OK;
}

void readBatteryState()
{
    // Prve citanie stabilizuje ADC po dlhsom intervale necinnosti.
    analogReadMilliVolts(BATTERY_ADC_PIN);
    delayMicroseconds(250);

    uint32_t totalMilliVolts = 0;

    for (uint8_t sample = 0; sample < BATTERY_SAMPLE_COUNT; sample++)
    {
        totalMilliVolts +=
            analogReadMilliVolts(BATTERY_ADC_PIN);

        delayMicroseconds(150);
    }

    const float adcMilliVolts =
        static_cast<float>(totalMilliVolts) /
        BATTERY_SAMPLE_COUNT;

    const float measuredVoltage =
        adcMilliVolts *
        BATTERY_DIVIDER_RATIO /
        1000.0F;

    if (
        isnan(measuredVoltage) ||
        measuredVoltage < 2.5F ||
        measuredVoltage > 4.5F
    )
    {
        batteryAvailable = false;
        batteryVoltage = NAN;
        batteryPercent = 0;

        Serial.println(
            "BATERIA: MERANIE NIE JE DOSTUPNE"
        );

        return;
    }

    batteryAvailable = true;

    if (isnan(batteryVoltage))
    {
        batteryVoltage = measuredVoltage;
    }
    else
    {
        // Jednoduche exponencialne vyhladenie ADC sumu.
        batteryVoltage =
            0.70F * batteryVoltage +
            0.30F * measuredVoltage;
    }

    batteryPercent =
        batteryPercentFromVoltage(batteryVoltage);

    Serial.printf(
        "BATERIA: %.2f V | %u %%\n",
        batteryVoltage,
        batteryPercent
    );
}

void updateBatteryWarning()
{
    uint8_t warningLevel = 0;

    if (batteryAvailable)
    {
        if (batteryPercent <= BATTERY_CRITICAL_PERCENT)
        {
            warningLevel = 2;
        }
        else if (batteryPercent <= BATTERY_WARNING_PERCENT)
        {
            warningLevel = 1;
        }
    }

    if (warningLevel == lastBatteryWarningLevel)
    {
        return;
    }

    lastBatteryWarningLevel = warningLevel;

    if (warningLevel == 2)
    {
        setStatusMessage(
            sessionActive
                ? "BATERIA KRITICKA - UKONCI RELACIU"
                : "BATERIA KRITICKA",
            COLOR_ERROR,
            6000
        );
    }
    else if (warningLevel == 1)
    {
        setStatusMessage(
            "NIZKA UROVEN BATERIE",
            COLOR_WARNING,
            5000
        );
    }
}

void initializeBatteryMonitor()
{
    pinMode(BATTERY_ADC_PIN, INPUT);
    analogReadResolution(12);
    analogSetPinAttenuation(
        BATTERY_ADC_PIN,
        ADC_11db
    );

    readBatteryState();
    updateBatteryWarning();
}

// ============================================================
// TRVALE NASTAVENIA A PODSVIETENIE
// ============================================================

bool valueIsAllowed(
    uint16_t value,
    const uint16_t *options,
    size_t optionCount
)
{
    for (size_t index = 0; index < optionCount; index++)
    {
        if (options[index] == value)
        {
            return true;
        }
    }

    return false;
}

bool brightnessIsAllowed(uint8_t value)
{
    return
        value >= MIN_BRIGHTNESS_PERCENT &&
        value <= MAX_BRIGHTNESS_PERCENT;
}

bool calibrationValueInRange(
    float value,
    float minimum,
    float maximum
)
{
    return
        isfinite(value) &&
        value >= minimum &&
        value <= maximum;
}

bool calibrationConfigIsValid(
    const CalibrationConfig &config
)
{
    return
        calibrationValueInRange(
            config.temperatureScale,
            MIN_CALIBRATION_SCALE,
            MAX_CALIBRATION_SCALE
        ) &&
        calibrationValueInRange(
            config.temperatureOffsetC,
            MIN_TEMPERATURE_OFFSET_C,
            MAX_TEMPERATURE_OFFSET_C
        ) &&
        calibrationValueInRange(
            config.humidityScale,
            MIN_CALIBRATION_SCALE,
            MAX_CALIBRATION_SCALE
        ) &&
        calibrationValueInRange(
            config.humidityOffsetPercent,
            MIN_HUMIDITY_OFFSET_PERCENT,
            MAX_HUMIDITY_OFFSET_PERCENT
        ) &&
        calibrationValueInRange(
            config.pressureScale,
            MIN_CALIBRATION_SCALE,
            MAX_CALIBRATION_SCALE
        ) &&
        calibrationValueInRange(
            config.pressureOffsetHpa,
            MIN_PRESSURE_OFFSET_HPA,
            MAX_PRESSURE_OFFSET_HPA
        );
}

void resetCalibrationConfig(
    CalibrationConfig &config
)
{
    config.enabled = false;
    config.temperatureScale =
        DEFAULT_CALIBRATION_SCALE;
    config.temperatureOffsetC =
        DEFAULT_CALIBRATION_OFFSET;
    config.humidityScale =
        DEFAULT_CALIBRATION_SCALE;
    config.humidityOffsetPercent =
        DEFAULT_CALIBRATION_OFFSET;
    config.pressureScale =
        DEFAULT_CALIBRATION_SCALE;
    config.pressureOffsetHpa =
        DEFAULT_CALIBRATION_OFFSET;
}

float applyLinearCalibration(
    float rawValue,
    float scale,
    float offset,
    bool enabled
)
{
    if (!enabled)
    {
        return rawValue;
    }

    return rawValue * scale + offset;
}

void loadPersistentSettings()
{
    preferences.begin("meteo", true);

    autoLogIntervalSeconds = preferences.getUShort(
        "log_seconds",
        DEFAULT_AUTO_LOG_INTERVAL_SECONDS
    );

    brightnessPercent = preferences.getUChar(
        "brightness",
        DEFAULT_BRIGHTNESS_PERCENT
    );

    const uint8_t storedAccentTheme =
        preferences.getUChar(
            "accent_theme",
            static_cast<uint8_t>(
                AccentTheme::Orange
            )
        );

    powerSavingEnabled = preferences.getBool(
        "power_save",
        DEFAULT_POWER_SAVING_ENABLED
    );

    powerDimTimeoutSeconds = preferences.getUShort(
        "power_dim_s",
        DEFAULT_POWER_DIM_TIMEOUT_SECONDS
    );

    calibration.enabled = preferences.getBool(
        "cal_enabled",
        false
    );

    calibration.temperatureScale = preferences.getFloat(
        "cal_t_a",
        DEFAULT_CALIBRATION_SCALE
    );

    calibration.temperatureOffsetC = preferences.getFloat(
        "cal_t_b",
        DEFAULT_CALIBRATION_OFFSET
    );

    calibration.humidityScale = preferences.getFloat(
        "cal_h_a",
        DEFAULT_CALIBRATION_SCALE
    );

    calibration.humidityOffsetPercent = preferences.getFloat(
        "cal_h_b",
        DEFAULT_CALIBRATION_OFFSET
    );

    calibration.pressureScale = preferences.getFloat(
        "cal_p_a",
        DEFAULT_CALIBRATION_SCALE
    );

    calibration.pressureOffsetHpa = preferences.getFloat(
        "cal_p_b",
        DEFAULT_CALIBRATION_OFFSET
    );

    preferences.end();

    if (!valueIsAllowed(
            autoLogIntervalSeconds,
            AUTO_LOG_INTERVAL_OPTIONS_SECONDS,
            AUTO_LOG_INTERVAL_OPTION_COUNT
        ))
    {
        autoLogIntervalSeconds =
            DEFAULT_AUTO_LOG_INTERVAL_SECONDS;
    }

    if (!brightnessIsAllowed(brightnessPercent))
    {
        brightnessPercent =
            DEFAULT_BRIGHTNESS_PERCENT;
    }

    if (!valueIsAllowed(
            powerDimTimeoutSeconds,
            POWER_DIM_TIMEOUT_OPTIONS_SECONDS,
            POWER_DIM_TIMEOUT_OPTION_COUNT
        ))
    {
        powerDimTimeoutSeconds =
            DEFAULT_POWER_DIM_TIMEOUT_SECONDS;
    }

    if (storedAccentTheme < ACCENT_THEME_COUNT)
    {
        accentTheme =
            static_cast<AccentTheme>(
                storedAccentTheme
            );
    }
    else
    {
        accentTheme =
            AccentTheme::Orange;
    }

    pendingAccentTheme = accentTheme;
    applyAccentTheme(accentTheme);

    pendingPowerSavingEnabled =
        powerSavingEnabled;

    pendingPowerDimTimeoutSeconds =
        powerDimTimeoutSeconds;

    if (!calibrationConfigIsValid(calibration))
    {
        resetCalibrationConfig(calibration);
    }

    pendingCalibration = calibration;
}

void saveGeneralPersistentSettings()
{
    preferences.begin("meteo", false);

    preferences.putUShort(
        "log_seconds",
        autoLogIntervalSeconds
    );

    preferences.putUChar(
        "brightness",
        brightnessPercent
    );

    preferences.end();
}

void saveAccentThemePersistentSettings()
{
    preferences.begin("meteo", false);

    preferences.putUChar(
        "accent_theme",
        static_cast<uint8_t>(
            accentTheme
        )
    );

    preferences.end();
}

void savePowerPersistentSettings()
{
    preferences.begin("meteo", false);

    preferences.putBool(
        "power_save",
        powerSavingEnabled
    );

    preferences.putUShort(
        "power_dim_s",
        powerDimTimeoutSeconds
    );

    preferences.end();
}

void saveCalibrationPersistentSettings()
{
    preferences.begin("meteo", false);

    preferences.putBool(
        "cal_enabled",
        calibration.enabled
    );

    preferences.putFloat(
        "cal_t_a",
        calibration.temperatureScale
    );

    preferences.putFloat(
        "cal_t_b",
        calibration.temperatureOffsetC
    );

    preferences.putFloat(
        "cal_h_a",
        calibration.humidityScale
    );

    preferences.putFloat(
        "cal_h_b",
        calibration.humidityOffsetPercent
    );

    preferences.putFloat(
        "cal_p_a",
        calibration.pressureScale
    );

    preferences.putFloat(
        "cal_p_b",
        calibration.pressureOffsetHpa
    );

    preferences.end();
}

uint32_t brightnessDuty(uint8_t percent)
{
    if (percent > 100)
    {
        percent = 100;
    }

    uint32_t duty =
        static_cast<uint32_t>(percent) * 255UL / 100UL;

#if defined(TFT_BACKLIGHT_ON) && TFT_BACKLIGHT_ON == LOW
    duty = 255UL - duty;
#endif

    return duty;
}

void applyBrightness(uint8_t percent)
{
    if (!displayPwmReady)
    {
        digitalWrite(
            TFT_BL,
            percent == 0
                ? !TFT_BACKLIGHT_ON
                : TFT_BACKLIGHT_ON
        );

        return;
    }

    const uint32_t duty =
        brightnessDuty(percent);

#if ESP_ARDUINO_VERSION_MAJOR >= 3
    ledcWrite(TFT_BL, duty);
#else
    ledcWrite(BACKLIGHT_PWM_CHANNEL, duty);
#endif
}

uint8_t activeAwakeBrightnessPercent()
{
    if (currentScreen == Screen::Settings)
    {
        return pendingBrightnessPercent;
    }

    return brightnessPercent;
}

void setDisplayPowerState(
    DisplayPowerState newState
)
{
    if (displayPowerState == newState)
    {
        return;
    }

    displayPowerState = newState;

    switch (displayPowerState)
    {
        case DisplayPowerState::Awake:
            applyBrightness(
                activeAwakeBrightnessPercent()
            );
            Serial.println(
                "DISPLEJ: AKTIVNY"
            );
            break;

        case DisplayPowerState::Dimmed:
            applyBrightness(
                POWER_DIM_BRIGHTNESS_PERCENT
            );
            Serial.println(
                "DISPLEJ: STLMENTY"
            );
            break;

        case DisplayPowerState::Off:
            applyBrightness(0);
            Serial.println(
                "DISPLEJ: VYPNUTY"
            );
            break;
    }
}

void registerUserActivity()
{
    lastUserActivityMillis = millis();

    if (
        displayPowerState !=
        DisplayPowerState::Awake
    )
    {
        setDisplayPowerState(
            DisplayPowerState::Awake
        );
    }
}

bool wakeDisplayAndConsumeTouch()
{
    if (
        displayPowerState ==
        DisplayPowerState::Awake
    )
    {
        lastUserActivityMillis = millis();
        return false;
    }

    registerUserActivity();

    // Prvy dotyk po stlmeni alebo vypnuti iba rozsvieti
    // displej. Ziadne tlacidlo sa tymto dotykom neaktivuje.
    return true;
}

void updateDisplayPowerSaving(
    uint32_t currentMillis
)
{
    // Pri aktivnom Wi-Fi exporte zostava displej rozsvieteny,
    // aby boli prihlasovacie udaje a stav prenosu stale viditelne.
    if (wifiExportRunning)
    {
        if (
            displayPowerState !=
            DisplayPowerState::Awake
        )
        {
            setDisplayPowerState(
                DisplayPowerState::Awake
            );
        }

        lastUserActivityMillis = currentMillis;
        return;
    }

    if (!powerSavingEnabled)
    {
        if (
            displayPowerState !=
            DisplayPowerState::Awake
        )
        {
            setDisplayPowerState(
                DisplayPowerState::Awake
            );
        }

        return;
    }

    const uint32_t idleMillis =
        currentMillis -
        lastUserActivityMillis;

    const uint32_t dimAfterMillis =
        static_cast<uint32_t>(
            powerDimTimeoutSeconds
        ) * 1000UL;

    const uint32_t offAfterMillis =
        dimAfterMillis +
        static_cast<uint32_t>(
            POWER_OFF_DELAY_SECONDS
        ) * 1000UL;

    if (idleMillis >= offAfterMillis)
    {
        setDisplayPowerState(
            DisplayPowerState::Off
        );
    }
    else if (idleMillis >= dimAfterMillis)
    {
        setDisplayPowerState(
            DisplayPowerState::Dimmed
        );
    }
    else
    {
        setDisplayPowerState(
            DisplayPowerState::Awake
        );
    }
}

void initializeBacklight()
{
    pinMode(TFT_BL, OUTPUT);

#if ESP_ARDUINO_VERSION_MAJOR >= 3
    displayPwmReady = ledcAttach(
        TFT_BL,
        BACKLIGHT_PWM_FREQUENCY,
        BACKLIGHT_PWM_RESOLUTION
    );
#else
    ledcSetup(
        BACKLIGHT_PWM_CHANNEL,
        BACKLIGHT_PWM_FREQUENCY,
        BACKLIGHT_PWM_RESOLUTION
    );

    ledcAttachPin(
        TFT_BL,
        BACKLIGHT_PWM_CHANNEL
    );

    displayPwmReady = true;
#endif

    applyBrightness(brightnessPercent);
}

// ============================================================
// DISPLEJ - ZAKLADNA INICIALIZACIA
// ============================================================

void initializeDisplay()
{
    tft.init();

    // Portretna orientacia, 90 stupnov proti smeru hodinovych
    // ruciciek oproti povodnej orientacii rotation = 1.
    tft.setRotation(0);

    initializeBacklight();

    tft.fillScreen(COLOR_BACKGROUND);
    tft.setTextDatum(MC_DATUM);
    tft.setTextColor(COLOR_TEXT, COLOR_BACKGROUND);

    tft.drawString(
        APP_NAME,
        tft.width() / 2,
        195,
        4
    );

    tft.setTextColor(COLOR_SECONDARY_TEXT, COLOR_BACKGROUND);

    tft.drawString(
        APP_VERSION,
        tft.width() / 2,
        235,
        2
    );

    tft.drawString(
        "Inicializacia...",
        tft.width() / 2,
        270,
        2
    );
}

void drawPanel(const Rect &rect, uint8_t radius = 8)
{
    tft.fillRoundRect(
        rect.x,
        rect.y,
        rect.width,
        rect.height,
        radius,
        COLOR_PANEL
    );

    tft.drawRoundRect(
        rect.x,
        rect.y,
        rect.width,
        rect.height,
        radius,
        COLOR_PANEL_BORDER
    );
}

void drawButton(
    const Rect &rect,
    const char *text,
    uint16_t fillColor,
    uint16_t borderColor,
    uint16_t textColor = COLOR_TEXT,
    uint8_t font = 2
)
{
    tft.fillRoundRect(
        rect.x,
        rect.y,
        rect.width,
        rect.height,
        7,
        fillColor
    );

    tft.drawRoundRect(
        rect.x,
        rect.y,
        rect.width,
        rect.height,
        7,
        borderColor
    );

    tft.setTextDatum(MC_DATUM);
    tft.setTextColor(textColor, fillColor);

    tft.drawString(
        text,
        rect.x + rect.width / 2,
        rect.y + rect.height / 2,
        font
    );
}

void drawColoredPanel(
    const Rect &rect,
    uint16_t fillColor,
    uint16_t borderColor,
    uint8_t radius = 8
)
{
    tft.fillRoundRect(
        rect.x,
        rect.y,
        rect.width,
        rect.height,
        radius,
        fillColor
    );

    tft.drawRoundRect(
        rect.x,
        rect.y,
        rect.width,
        rect.height,
        radius,
        borderColor
    );
}

void invalidateMainUiCaches()
{
    mainDateTimeCacheValid = false;
    mainMeasurementCacheValid = false;
    mainStatusCacheValid = false;
    mainMessageCacheValid = false;
    mainSaveButtonCacheValid = false;

    cachedMainDate[0] = '\0';
    cachedMainTime[0] = '\0';
    cachedMainBattery[0] = '\0';

    cachedTemperatureValue[0] = '\0';
    cachedHumidityValue[0] = '\0';
    cachedPressureValue[0] = '\0';

    cachedMainStatusSignature[0] = '\0';
    cachedMainMessageSignature[0] = '\0';
    cachedSaveButtonText[0] = '\0';
}


// ============================================================
// HLAVNA OBRAZOVKA - STATICKY VZHLAD
// ============================================================

void drawMainStaticLayout()
{
    invalidateMainUiCaches();

    tft.fillScreen(COLOR_BACKGROUND);

    // Datum a cas.
    tft.fillRect(0, 0, 320, 40, COLOR_PANEL);
    tft.drawFastHLine(0, 39, 320, COLOR_PANEL_BORDER);

    // Atmosfericke hodnoty - vyrazne oranzove panely.
    drawColoredPanel(
        Rect{10, 48, 300, 74},
        COLOR_PRIMARY,
        COLOR_ACCENT
    );

    drawColoredPanel(
        Rect{10, 130, 145, 64},
        COLOR_PRIMARY,
        COLOR_ACCENT
    );

    drawColoredPanel(
        Rect{165, 130, 145, 64},
        COLOR_PRIMARY,
        COLOR_ACCENT
    );

    // Stanovisko a merany bod.
    drawPanel(STATION_FIELD_RECT);
    drawPanel(TARGET_FIELD_RECT);

    tft.setTextDatum(TL_DATUM);
    tft.setTextColor(TFT_BLACK, COLOR_PRIMARY);

    // Teplotna jednotka so samostatne vykreslenym znakom stupna.
    const char *temperatureLabelStart = "TEPLOTA (";
    constexpr int16_t temperatureLabelX = 20;
    constexpr int16_t temperatureLabelY = 56;

    tft.drawString(
        temperatureLabelStart,
        temperatureLabelX,
        temperatureLabelY,
        1
    );

    const int16_t degreeX =
        temperatureLabelX +
        tft.textWidth(temperatureLabelStart, 1) +
        2;

    tft.drawCircle(
        degreeX,
        temperatureLabelY + 2,
        2,
        TFT_BLACK
    );

    tft.drawString(
        "C)",
        degreeX + 5,
        temperatureLabelY,
        1
    );

    tft.drawString("VLHKOST (%)", 20, 138, 2);
    tft.drawString("TLAK (hPa)", 175, 138, 2);

    // Stav zariadenia a pocet manualnych zaznamov.
    drawPanel(Rect{10, 402, 300, 36});

    // Spodny informacny riadok a zvacsene skratky.
    tft.fillRect(0, 440, 320, 40, COLOR_BACKGROUND);
}

// ============================================================
// HLAVNA OBRAZOVKA - DATUM A CAS
// ============================================================

void drawBatteryHeaderStatus()
{
    char batteryBuffer[20];

    if (batteryAvailable)
    {
        snprintf(
            batteryBuffer,
            sizeof(batteryBuffer),
            "%u%% %.2f V",
            batteryPercent,
            batteryVoltage
        );
    }
    else
    {
        snprintf(
            batteryBuffer,
            sizeof(batteryBuffer),
            "--%% --.--V"
        );
    }

    const uint16_t color =
        batteryStatusColor();

    if (
        mainDateTimeCacheValid &&
        strcmp(
            cachedMainBattery,
            batteryBuffer
        ) == 0 &&
        cachedMainBatteryColor == color
    )
    {
        return;
    }

    tft.fillRect(
        214,
        4,
        100,
        32,
        COLOR_PANEL
    );

    tft.setTextDatum(MR_DATUM);
    tft.setTextColor(color, COLOR_PANEL);

    tft.drawString(
        batteryBuffer,
        314,
        20,
        2
    );

    snprintf(
        cachedMainBattery,
        sizeof(cachedMainBattery),
        "%s",
        batteryBuffer
    );

    cachedMainBatteryColor = color;
}

void updateDateTimeDisplay(const DateTime &dateTime)
{
    char dateBuffer[16];
    char timeBuffer[16];

    snprintf(
        dateBuffer,
        sizeof(dateBuffer),
        "%02u.%02u.%04u",
        dateTime.day(),
        dateTime.month(),
        dateTime.year()
    );

    snprintf(
        timeBuffer,
        sizeof(timeBuffer),
        "%02u:%02u:%02u",
        dateTime.hour(),
        dateTime.minute(),
        dateTime.second()
    );

    if (
        !mainDateTimeCacheValid ||
        strcmp(cachedMainDate, dateBuffer) != 0
    )
    {
        tft.fillRect(6, 4, 112, 32, COLOR_PANEL);

        tft.setTextColor(COLOR_TEXT, COLOR_PANEL);
        tft.setTextDatum(ML_DATUM);

        tft.drawString(
            dateBuffer,
            8,
            20,
            2
        );

        snprintf(
            cachedMainDate,
            sizeof(cachedMainDate),
            "%s",
            dateBuffer
        );
    }

    if (
        !mainDateTimeCacheValid ||
        strcmp(cachedMainTime, timeBuffer) != 0
    )
    {
        tft.fillRect(118, 4, 96, 32, COLOR_PANEL);

        tft.setTextColor(COLOR_TEXT, COLOR_PANEL);
        tft.setTextDatum(MC_DATUM);

        tft.drawString(
            timeBuffer,
            166,
            20,
            2
        );

        snprintf(
            cachedMainTime,
            sizeof(cachedMainTime),
            "%s",
            timeBuffer
        );
    }

    drawBatteryHeaderStatus();

    mainDateTimeCacheValid = true;
}

// ============================================================
// HLAVNA OBRAZOVKA - HODNOTY
// ============================================================

void drawCenteredValue(
    const Rect &rect,
    const char *value,
    uint8_t font,
    uint8_t textSize = 1
)
{
    tft.fillRect(
        rect.x,
        rect.y,
        rect.width,
        rect.height,
        COLOR_PRIMARY
    );

    tft.setTextDatum(MC_DATUM);
    tft.setTextColor(TFT_BLACK, COLOR_PRIMARY);
    tft.setTextSize(textSize);

    const int16_t centerX =
        rect.x + rect.width / 2;

    const int16_t centerY =
        rect.y + rect.height / 2;

    // Jemny bold efekt bez obrysu: text sa vykresli dvakrat
    // s horizontalnym posunom jedneho pixelu.
    tft.drawString(
        value,
        centerX - 1,
        centerY,
        font
    );

    tft.drawString(
        value,
        centerX,
        centerY,
        font
    );

    tft.setTextSize(1);
}

void updateMeasurementDisplay(const Measurement &measurement)
{
    char temperatureBuffer[24];
    char humidityBuffer[24];
    char pressureBuffer[24];

    if (!measurement.valid)
    {
        snprintf(
            temperatureBuffer,
            sizeof(temperatureBuffer),
            "---"
        );

        snprintf(
            humidityBuffer,
            sizeof(humidityBuffer),
            "---"
        );

        snprintf(
            pressureBuffer,
            sizeof(pressureBuffer),
            "---"
        );
    }
    else
    {
        snprintf(
            temperatureBuffer,
            sizeof(temperatureBuffer),
            "%.2f",
            measurement.temperatureC
        );

        snprintf(
            humidityBuffer,
            sizeof(humidityBuffer),
            "%.2f",
            measurement.humidityPercent
        );

        snprintf(
            pressureBuffer,
            sizeof(pressureBuffer),
            "%.2f",
            measurement.pressureHpa
        );
    }

    if (
        !mainMeasurementCacheValid ||
        strcmp(
            cachedTemperatureValue,
            temperatureBuffer
        ) != 0
    )
    {
        drawCenteredValue(
            Rect{20, 68, 280, 50},
            temperatureBuffer,
            6
        );

        snprintf(
            cachedTemperatureValue,
            sizeof(cachedTemperatureValue),
            "%s",
            temperatureBuffer
        );
    }

    if (
        !mainMeasurementCacheValid ||
        strcmp(
            cachedHumidityValue,
            humidityBuffer
        ) != 0
    )
    {
        drawCenteredValue(
            Rect{20, 156, 125, 28},
            humidityBuffer,
            4
        );

        snprintf(
            cachedHumidityValue,
            sizeof(cachedHumidityValue),
            "%s",
            humidityBuffer
        );
    }

    if (
        !mainMeasurementCacheValid ||
        strcmp(
            cachedPressureValue,
            pressureBuffer
        ) != 0
    )
    {
        drawCenteredValue(
            Rect{175, 156, 125, 28},
            pressureBuffer,
            4
        );

        snprintf(
            cachedPressureValue,
            sizeof(cachedPressureValue),
            "%s",
            pressureBuffer
        );
    }

    mainMeasurementCacheValid = true;
}

// ============================================================
// HLAVNA OBRAZOVKA - EDITOVATELNE POLIA
// ============================================================

void drawEditableField(
    const Rect &rect,
    const char *label,
    const char *value,
    const char *emptyText,
    bool editable
)
{
    const uint16_t borderColor =
        editable ? COLOR_PANEL_BORDER : COLOR_DISABLED;

    tft.fillRoundRect(
        rect.x + 1,
        rect.y + 1,
        rect.width - 2,
        rect.height - 2,
        7,
        COLOR_PANEL
    );

    tft.drawRoundRect(
        rect.x,
        rect.y,
        rect.width,
        rect.height,
        8,
        borderColor
    );

    tft.setTextDatum(TL_DATUM);
    tft.setTextColor(COLOR_SECONDARY_TEXT, COLOR_PANEL);
    tft.drawString(label, rect.x + 10, rect.y + 5, 1);

    tft.setTextDatum(ML_DATUM);

    if (identifierIsEmpty(value))
    {
        tft.setTextColor(
            editable ? COLOR_WARNING : COLOR_DISABLED,
            COLOR_PANEL
        );

        tft.drawString(
            emptyText,
            rect.x + 10,
            rect.y + 27,
            2
        );
    }
    else
    {
        tft.setTextColor(COLOR_TEXT, COLOR_PANEL);
        tft.drawString(
            value,
            rect.x + 10,
            rect.y + 27,
            2
        );
    }

    tft.setTextDatum(MR_DATUM);
    tft.setTextColor(
        editable ? COLOR_PRIMARY : COLOR_DISABLED,
        COLOR_PANEL
    );

    tft.drawString(
        editable ? "UPRAV" : "ZAMKNUTE",
        rect.x + rect.width - 10,
        rect.y + 27,
        1
    );
}

void updateEditableFields()
{
    drawEditableField(
        STATION_FIELD_RECT,
        "STANOVISKO",
        station,
        "NOVA RELACIA",
        !sessionActive
    );

    drawEditableField(
        TARGET_FIELD_RECT,
        "MERANY BOD",
        targetPoint,
        sessionActive
            ? "DOTYKOM ZADAJ"
            : "NAJPRV RELACIA",
        sessionActive
    );
}

// ============================================================
// HLAVNA OBRAZOVKA - STAVOVE INDIKATORY
// ============================================================

uint16_t statusColor(StatusState state)
{
    switch (state)
    {
        case StatusState::Ok:
            return STATUS_COLOR_OK;

        case StatusState::Warning:
            return STATUS_COLOR_WARNING;

        case StatusState::Error:
        default:
            return STATUS_COLOR_ERROR;
    }
}

void drawCompactStatus(
    int16_t centerX,
    int16_t centerY,
    const char *label,
    int8_t acuteAccentIndex,
    StatusState state
)
{
    const uint16_t color = statusColor(state);

    tft.fillCircle(centerX, centerY - 7, 5, color);

    const int16_t labelY = centerY + 4;

    tft.setTextDatum(TC_DATUM);
    tft.setTextColor(COLOR_SECONDARY_TEXT, COLOR_PANEL);
    tft.drawString(label, centerX, labelY, 1);

    // Vstavany font nema plnu podporu UTF-8. Pre dve stavove
    // slova preto vykreslime dlzen/ciarku nad pismenom A rucne.
    if (acuteAccentIndex >= 0)
    {
        char prefix[16];

        const size_t prefixLength =
            static_cast<size_t>(
                acuteAccentIndex
            );

        snprintf(
            prefix,
            sizeof(prefix),
            "%.*s",
            static_cast<int>(prefixLength),
            label
        );

        const int16_t labelWidth =
            tft.textWidth(label, 1);

        const int16_t prefixWidth =
            tft.textWidth(prefix, 1);

        const int16_t letterWidth =
            tft.textWidth("A", 1);

        const int16_t accentX =
            centerX -
            labelWidth / 2 +
            prefixWidth +
            letterWidth / 2;

        tft.drawPixel(
            accentX,
            labelY - 2,
            COLOR_SECONDARY_TEXT
        );

        tft.drawPixel(
            accentX + 1,
            labelY - 3,
            COLOR_SECONDARY_TEXT
        );
    }
}

void updateStatusPanel()
{
    StatusState autoState = StatusState::Warning;

    if (sessionActive)
    {
        autoState =
            lastAutoWriteOk
                ? StatusState::Ok
                : StatusState::Error;
    }

    char signature[64];

    snprintf(
        signature,
        sizeof(signature),
        "%u|%u|%u|%u|%u|%u|%lu",
        sensorsAreReady() ? 1U : 0U,
        sdReady ? 1U : 0U,
        sdSpaceLow ? 1U : 0U,
        sdSpaceCritical ? 1U : 0U,
        sessionActive ? 1U : 0U,
        static_cast<unsigned int>(autoState),
        static_cast<unsigned long>(
            manualRecordCount
        )
    );

    if (
        mainStatusCacheValid &&
        strcmp(
            cachedMainStatusSignature,
            signature
        ) == 0
    )
    {
        return;
    }

    tft.fillRoundRect(11, 403, 298, 34, 7, COLOR_PANEL);

    drawCompactStatus(
        31,
        420,
        "SENZOR",
        -1,
        sensorsAreReady()
            ? StatusState::Ok
            : StatusState::Error
    );

    drawCompactStatus(
        82,
        420,
        "SD",
        -1,
        !sdReady ||
        sdSpaceCritical
            ? StatusState::Error
            : sdSpaceLow
                ? StatusState::Warning
                : StatusState::Ok
    );

    drawCompactStatus(
        144,
        420,
        "RELACIA",
        3,
        sessionActive
            ? StatusState::Ok
            : StatusState::Warning
    );

    drawCompactStatus(
        209,
        420,
        "ZAZNAM",
        1,
        autoState
    );

    char countLabel[24];

    snprintf(
        countLabel,
        sizeof(countLabel),
        "MANUAL: %lu",
        static_cast<unsigned long>(
            manualRecordCount
        )
    );

    tft.setTextDatum(MC_DATUM);
    tft.setTextColor(
        sessionActive
            ? COLOR_TEXT
            : COLOR_DISABLED,
        COLOR_PANEL
    );

    tft.drawString(
        countLabel,
        270,
        420,
        1
    );

    snprintf(
        cachedMainStatusSignature,
        sizeof(cachedMainStatusSignature),
        "%s",
        signature
    );

    mainStatusCacheValid = true;
}

// ============================================================
// HLAVNA OBRAZOVKA - INFORMACNY RIADOK
// ============================================================

void drawMsbBitmap(
    int16_t x,
    int16_t y,
    const uint8_t *bitmap,
    uint8_t width,
    uint8_t height,
    uint16_t foregroundColor,
    uint16_t backgroundColor
)
{
    const uint8_t bytesPerRow =
        (width + 7) / 8;

    // Pozadie tlacidla zostava cierne.
    tft.fillRect(
        x,
        y,
        width,
        height,
        backgroundColor
    );

    for (uint8_t row = 0; row < height; row++)
    {
        for (uint8_t column = 0; column < width; column++)
        {
            const uint8_t byteValue =
                pgm_read_byte(
                    bitmap +
                    row * bytesPerRow +
                    column / 8
                );

            const bool sourceBitIsSet =
                byteValue &
                (0x80U >> (column % 8));

            // Nastavene bity tvoria oranzove ozubene koliesko.
            if (sourceBitIsSet)
            {
                tft.drawPixel(
                    x + column,
                    y + row,
                    foregroundColor
                );
            }
        }
    }
}

void drawScaledMsbBitmap(
    int16_t x,
    int16_t y,
    const uint8_t *bitmap,
    uint8_t sourceWidth,
    uint8_t sourceHeight,
    uint8_t destinationWidth,
    uint8_t destinationHeight,
    uint16_t foregroundColor,
    uint16_t backgroundColor
)
{
    const uint8_t bytesPerRow =
        (sourceWidth + 7) / 8;

    tft.fillRect(
        x,
        y,
        destinationWidth,
        destinationHeight,
        backgroundColor
    );

    for (
        uint8_t destinationY = 0;
        destinationY < destinationHeight;
        destinationY++
    )
    {
        const uint8_t sourceY =
            static_cast<uint8_t>(
                (
                    static_cast<uint16_t>(
                        destinationY
                    ) *
                    sourceHeight
                ) /
                destinationHeight
            );

        for (
            uint8_t destinationX = 0;
            destinationX < destinationWidth;
            destinationX++
        )
        {
            const uint8_t sourceX =
                static_cast<uint8_t>(
                    (
                        static_cast<uint16_t>(
                            destinationX
                        ) *
                        sourceWidth
                    ) /
                    destinationWidth
                );

            const uint8_t byteValue =
                pgm_read_byte(
                    bitmap +
                    sourceY * bytesPerRow +
                    sourceX / 8
                );

            if (
                byteValue &
                (0x80U >> (sourceX % 8))
            )
            {
                tft.drawPixel(
                    x + destinationX,
                    y + destinationY,
                    foregroundColor
                );
            }
        }
    }
}


void drawSettingsGearIcon()
{
    if (currentScreen != Screen::Main)
    {
        return;
    }

    const int16_t iconX =
        SETTINGS_SHORTCUT_RECT.x +
        (
            SETTINGS_SHORTCUT_RECT.width -
            MAIN_SHORTCUT_ICON_SIZE
        ) / 2;

    const int16_t iconY =
        SETTINGS_SHORTCUT_RECT.y +
        (
            SETTINGS_SHORTCUT_RECT.height -
            MAIN_SHORTCUT_ICON_SIZE
        ) / 2;

    drawScaledMsbBitmap(
        iconX,
        iconY,
        SETTINGS_GEAR_BITMAP,
        SETTINGS_GEAR_BITMAP_WIDTH,
        SETTINGS_GEAR_BITMAP_HEIGHT,
        MAIN_SHORTCUT_ICON_SIZE,
        MAIN_SHORTCUT_ICON_SIZE,
        COLOR_PRIMARY,
        COLOR_BACKGROUND
    );
}


void drawWifiShortcutIcon()
{
    if (currentScreen != Screen::Main)
    {
        return;
    }

    uint16_t color =
        (
            sdReady &&
            !sessionActive
        )
            ? COLOR_PRIMARY
            : COLOR_DISABLED;

    if (wifiExportRunning)
    {
        color =
            WiFi.softAPgetStationNum() > 0
                ? COLOR_OK
                : COLOR_ACCENT;
    }

    const int16_t iconX =
        WIFI_SHORTCUT_RECT.x +
        (
            WIFI_SHORTCUT_RECT.width -
            MAIN_SHORTCUT_ICON_SIZE
        ) / 2;

    const int16_t iconY =
        WIFI_SHORTCUT_RECT.y +
        (
            WIFI_SHORTCUT_RECT.height -
            MAIN_SHORTCUT_ICON_SIZE
        ) / 2;

    drawScaledMsbBitmap(
        iconX,
        iconY,
        WIFI_BITMAP,
        WIFI_BITMAP_WIDTH,
        WIFI_BITMAP_HEIGHT,
        MAIN_SHORTCUT_ICON_SIZE,
        MAIN_SHORTCUT_ICON_SIZE,
        color,
        COLOR_BACKGROUND
    );
}

void drawArchiveShortcutIcon()
{
    if (currentScreen != Screen::Main)
    {
        return;
    }

    const int16_t iconX =
        ARCHIVE_SHORTCUT_RECT.x +
        (
            ARCHIVE_SHORTCUT_RECT.width -
            MAIN_SHORTCUT_ICON_SIZE
        ) / 2;

    const int16_t iconY =
        ARCHIVE_SHORTCUT_RECT.y +
        (
            ARCHIVE_SHORTCUT_RECT.height -
            MAIN_SHORTCUT_ICON_SIZE
        ) / 2;

    drawScaledMsbBitmap(
        iconX,
        iconY,
        ARCHIVE_BITMAP,
        ARCHIVE_BITMAP_WIDTH,
        ARCHIVE_BITMAP_HEIGHT,
        MAIN_SHORTCUT_ICON_SIZE,
        MAIN_SHORTCUT_ICON_SIZE,
        sdReady ? COLOR_PRIMARY : COLOR_DISABLED,
        COLOR_BACKGROUND
    );
}


void drawGraphShortcutIcon()
{
    if (currentScreen != Screen::Main)
    {
        return;
    }

    const int16_t iconX =
        GRAPH_SHORTCUT_RECT.x +
        (
            GRAPH_SHORTCUT_RECT.width -
            MAIN_SHORTCUT_ICON_SIZE
        ) / 2;

    const int16_t iconY =
        GRAPH_SHORTCUT_RECT.y +
        (
            GRAPH_SHORTCUT_RECT.height -
            MAIN_SHORTCUT_ICON_SIZE
        ) / 2;

    drawScaledMsbBitmap(
        iconX,
        iconY,
        GRAPH_BITMAP,
        GRAPH_BITMAP_WIDTH,
        GRAPH_BITMAP_HEIGHT,
        MAIN_SHORTCUT_ICON_SIZE,
        MAIN_SHORTCUT_ICON_SIZE,
        sessionActive ? COLOR_PRIMARY : COLOR_DISABLED,
        COLOR_BACKGROUND
    );
}

void updateMessageStrip()
{
    const char *message = statusMessage;
    uint16_t color = statusMessageColor;

    if (
        statusMessage[0] != '\0' &&
        statusMessageUntil != 0 &&
        !timedEventActive(statusMessageUntil)
    )
    {
        clearStatusMessage();
        message = "";
    }

    if (message[0] == '\0')
    {
        if (!sdReady)
        {
            message = "SD KARTA NIE JE DOSTUPNA";
            color = COLOR_ERROR;
        }
        else if (!sensorsAreReady())
        {
            message = "CHYBA MERACICH ZARIADENI";
            color = COLOR_ERROR;
        }
        else if (!currentMeasurement.valid)
        {
            message = measurementErrorText(
                lastMeasurementError
            );

            color = COLOR_ERROR;
        }
        else if (
            batteryAvailable &&
            batteryPercent <=
                BATTERY_CRITICAL_PERCENT
        )
        {
            message = sessionActive
                ? "BATERIA KRITICKA - UKONCI RELACIU"
                : "BATERIA KRITICKA";

            color = COLOR_ERROR;
        }
        else if (
            batteryAvailable &&
            batteryPercent <=
                BATTERY_WARNING_PERCENT
        )
        {
            message = "NIZKA UROVEN BATERIE";
            color = COLOR_WARNING;
        }
        else if (!sessionActive)
        {
            message = "STLAC NOVA RELACIA";
            color = COLOR_WARNING;
        }
        else if (identifierIsEmpty(targetPoint))
        {
            message = "ZADAJ MERANY BOD";
            color = COLOR_WARNING;
        }
        else
        {
            message = "PRIPRAVENE NA ZAZNAM";
            color = COLOR_SECONDARY_TEXT;
        }
    }

    char signature[96];

    snprintf(
        signature,
        sizeof(signature),
        "%s|%u|%u|%u|%u|%u",
        message,
        static_cast<unsigned int>(color),
        sdReady ? 1U : 0U,
        sessionActive ? 1U : 0U,
        wifiExportRunning ? 1U : 0U,
        static_cast<unsigned int>(
            wifiExportRunning
                ? WiFi.softAPgetStationNum()
                : 0
        )
    );

    if (
        mainMessageCacheValid &&
        strcmp(
            cachedMainMessageSignature,
            signature
        ) == 0
    )
    {
        return;
    }

    tft.fillRect(
        STATUS_MESSAGE_RECT.x,
        STATUS_MESSAGE_RECT.y,
        STATUS_MESSAGE_RECT.width,
        STATUS_MESSAGE_RECT.height,
        COLOR_BACKGROUND
    );

    const int16_t maximumTextWidth =
        STATUS_MESSAGE_RECT.width - 8;

    tft.setTextColor(
        color,
        COLOR_BACKGROUND
    );

    if (
        tft.textWidth(message, 2) <=
        maximumTextWidth
    )
    {
        tft.setTextDatum(MC_DATUM);

        tft.drawString(
            message,
            STATUS_MESSAGE_RECT.x +
                STATUS_MESSAGE_RECT.width / 2,
            STATUS_MESSAGE_RECT.y +
                STATUS_MESSAGE_RECT.height / 2,
            2
        );
    }
    else
    {
        char firstLine[40] = "";
        char secondLine[40] = "";

        const size_t messageLength =
            strlen(message);

        int16_t bestSplit = -1;
        int16_t bestDifference = 32767;

        for (
            size_t index = 1;
            index < messageLength;
            index++
        )
        {
            if (message[index] != ' ')
            {
                continue;
            }

            char leftCandidate[40];
            char rightCandidate[40];

            snprintf(
                leftCandidate,
                sizeof(leftCandidate),
                "%.*s",
                static_cast<int>(index),
                message
            );

            snprintf(
                rightCandidate,
                sizeof(rightCandidate),
                "%s",
                message + index + 1
            );

            const int16_t leftWidth =
                tft.textWidth(
                    leftCandidate,
                    1
                );

            const int16_t rightWidth =
                tft.textWidth(
                    rightCandidate,
                    1
                );

            if (
                leftWidth <= maximumTextWidth &&
                rightWidth <= maximumTextWidth
            )
            {
                const int16_t difference =
                    abs(leftWidth - rightWidth);

                if (difference < bestDifference)
                {
                    bestDifference = difference;
                    bestSplit =
                        static_cast<int16_t>(
                            index
                        );
                }
            }
        }

        if (bestSplit >= 0)
        {
            snprintf(
                firstLine,
                sizeof(firstLine),
                "%.*s",
                bestSplit,
                message
            );

            snprintf(
                secondLine,
                sizeof(secondLine),
                "%s",
                message + bestSplit + 1
            );
        }
        else
        {
            snprintf(
                firstLine,
                sizeof(firstLine),
                "%s",
                message
            );

            while (
                strlen(firstLine) > 3 &&
                tft.textWidth(
                    firstLine,
                    1
                ) > maximumTextWidth
            )
            {
                firstLine[
                    strlen(firstLine) - 1
                ] = '\0';
            }

            if (strlen(firstLine) > 3)
            {
                const size_t length =
                    strlen(firstLine);

                firstLine[length - 3] = '.';
                firstLine[length - 2] = '.';
                firstLine[length - 1] = '.';
            }
        }

        tft.setTextDatum(MC_DATUM);

        tft.drawString(
            firstLine,
            STATUS_MESSAGE_RECT.x +
                STATUS_MESSAGE_RECT.width / 2,
            STATUS_MESSAGE_RECT.y + 11,
            1
        );

        if (secondLine[0] != '\0')
        {
            tft.drawString(
                secondLine,
                STATUS_MESSAGE_RECT.x +
                    STATUS_MESSAGE_RECT.width / 2,
                STATUS_MESSAGE_RECT.y + 28,
                1
            );
        }
    }

    drawWifiShortcutIcon();
    drawArchiveShortcutIcon();
    drawGraphShortcutIcon();
    drawSettingsGearIcon();

    snprintf(
        cachedMainMessageSignature,
        sizeof(cachedMainMessageSignature),
        "%s",
        signature
    );

    mainMessageCacheValid = true;
}

// ============================================================
// HLAVNA OBRAZOVKA - RIADENIE RELACIE
// ============================================================

void drawSessionButtons()
{
    const bool startBlocked =
        !sessionActive &&
        (
            !sdReady ||
            sdSpaceCritical
        );

    drawButton(
        SESSION_TOGGLE_BUTTON_RECT,
        sessionActive
            ? "UKONCIT RELACIU"
            : startBlocked
                ? "SD KARTA NEMA MIESTO"
                : "SPUSTIT RELACIU",
        sessionActive
            ? COLOR_PANEL
            : startBlocked
                ? COLOR_BACKGROUND
                : COLOR_PRIMARY,
        sessionActive
            ? COLOR_WARNING
            : startBlocked
                ? COLOR_ERROR
                : COLOR_PRIMARY,
        sessionActive
            ? COLOR_TEXT
            : startBlocked
                ? COLOR_ERROR
                : TFT_BLACK,
        startBlocked
            ? 1
            : 2
    );
}

// ============================================================
// HLAVNA OBRAZOVKA - TLACIDLO ULOZENIA
// ============================================================

void drawSaveButton()
{
    uint16_t fillColor = COLOR_BACKGROUND;
    uint16_t borderColor = COLOR_DISABLED;
    const char *buttonText = "ULOZENIE NEDOSTUPNE";

    if (saveButtonState == SaveButtonState::Success)
    {
        fillColor = COLOR_OK;
        borderColor = COLOR_OK;
        buttonText = "MERANIE ULOZENE";
    }
    else if (saveButtonState == SaveButtonState::Error)
    {
        fillColor = COLOR_ERROR;
        borderColor = COLOR_ERROR;
        buttonText = "CHYBA ZAPISU";
    }
    else if (manualSaveAvailable())
    {
        fillColor = COLOR_PANEL;
        borderColor = COLOR_PRIMARY;
        buttonText = "ULOZIT MERANIE";
    }
    else if (sdSpaceCritical)
    {
        borderColor = COLOR_ERROR;
        buttonText = "SD KARTA JE PLNA";
    }
    else if (!sessionActive)
    {
        buttonText = "NAJPRV STANOVISKO";
    }
    else if (identifierIsEmpty(targetPoint))
    {
        buttonText = "NAJPRV MERANY BOD";
    }

    if (
        mainSaveButtonCacheValid &&
        strcmp(
            cachedSaveButtonText,
            buttonText
        ) == 0 &&
        cachedSaveFillColor == fillColor &&
        cachedSaveBorderColor == borderColor
    )
    {
        return;
    }

    drawButton(
        SAVE_BUTTON_RECT,
        buttonText,
        fillColor,
        borderColor,
        COLOR_TEXT,
        2
    );

    snprintf(
        cachedSaveButtonText,
        sizeof(cachedSaveButtonText),
        "%s",
        buttonText
    );

    cachedSaveFillColor = fillColor;
    cachedSaveBorderColor = borderColor;
    mainSaveButtonCacheValid = true;
}

void drawMainScreen()
{
    currentScreen = Screen::Main;

    drawMainStaticLayout();
    updateDateTimeDisplay(currentMeasurement.timestamp);
    updateMeasurementDisplay(currentMeasurement);
    updateEditableFields();
    drawSessionButtons();
    drawSaveButton();
    updateStatusPanel();
    updateMessageStrip();
}

void updateMainScreen()
{
    if (currentScreen != Screen::Main)
    {
        return;
    }

    // Prekresluju sa iba dynamicke oblasti, nie cela obrazovka.
    updateDateTimeDisplay(
        currentMeasurement.timestamp
    );

    updateMeasurementDisplay(
        currentMeasurement
    );

    drawSaveButton();
    updateStatusPanel();
    updateMessageStrip();
}


// ============================================================
// GRAFY RELACIE - POMOCNE FUNKCIE
// ============================================================

void resetGraphStatistics(GraphStatistics &statistics)
{
    statistics.minimum = INFINITY;
    statistics.maximum = -INFINITY;
    statistics.sum = 0.0;
    statistics.count = 0;
}

void addGraphStatistic(
    GraphStatistics &statistics,
    float value
)
{
    if (!isfinite(value))
    {
        return;
    }

    if (value < statistics.minimum)
    {
        statistics.minimum = value;
    }

    if (value > statistics.maximum)
    {
        statistics.maximum = value;
    }

    statistics.sum += value;
    statistics.count++;
}

float graphAverage(const GraphStatistics &statistics)
{
    if (statistics.count == 0)
    {
        return NAN;
    }

    return static_cast<float>(
        statistics.sum /
        static_cast<double>(statistics.count)
    );
}

void resetAllGraphStatistics()
{
    resetGraphStatistics(
        graphDisplayTemperatureStats
    );

    resetGraphStatistics(
        graphDisplayHumidityStats
    );

    resetGraphStatistics(
        graphDisplayPressureStats
    );

    resetGraphStatistics(
        graphTotalTemperatureStats
    );

    resetGraphStatistics(
        graphTotalHumidityStats
    );

    resetGraphStatistics(
        graphTotalPressureStats
    );
}

void addSampleToStatistics(
    const GraphSample &sample,
    GraphStatistics &temperatureStats,
    GraphStatistics &humidityStats,
    GraphStatistics &pressureStats
)
{
    addGraphStatistic(
        temperatureStats,
        sample.temperatureC
    );

    addGraphStatistic(
        humidityStats,
        sample.humidityPercent
    );

    addGraphStatistic(
        pressureStats,
        sample.pressureHpa
    );
}

bool readCsvLine(
    File &file,
    char *buffer,
    size_t bufferSize
)
{
    if (
        !file.available() ||
        bufferSize < 2
    )
    {
        return false;
    }

    size_t length = 0;

    while (file.available())
    {
        const int value = file.read();

        if (value < 0)
        {
            break;
        }

        const char character =
            static_cast<char>(value);

        if (character == '\n')
        {
            break;
        }

        if (character == '\r')
        {
            continue;
        }

        if (length + 1 < bufferSize)
        {
            buffer[length++] = character;
        }
    }

    buffer[length] = '\0';

    return true;
}

size_t splitCsvFields(
    char *line,
    char **fields,
    size_t maximumFields
)
{
    if (
        line == nullptr ||
        fields == nullptr ||
        maximumFields == 0
    )
    {
        return 0;
    }

    char *source = line;
    char *destination = line;

    size_t fieldCount = 1;
    fields[0] = destination;

    bool insideQuotes = false;

    while (*source != '\0')
    {
        const char character = *source++;

        if (insideQuotes)
        {
            if (character == '"')
            {
                if (*source == '"')
                {
                    *destination++ = '"';
                    source++;
                }
                else
                {
                    insideQuotes = false;
                }
            }
            else
            {
                *destination++ = character;
            }

            continue;
        }

        if (
            character == '"' &&
            destination == fields[fieldCount - 1]
        )
        {
            insideQuotes = true;
        }
        else if (character == ',')
        {
            *destination++ = '\0';

            if (fieldCount < maximumFields)
            {
                fields[fieldCount++] = destination;
            }
        }
        else
        {
            *destination++ = character;
        }
    }

    *destination = '\0';

    return fieldCount;
}

bool parseIsoTimestamp(
    const char *timestampText,
    uint32_t &unixTime
)
{
    unsigned int year = 0;
    unsigned int month = 0;
    unsigned int day = 0;
    unsigned int hour = 0;
    unsigned int minute = 0;
    unsigned int second = 0;

    const int parsed = sscanf(
        timestampText,
        "%4u-%2u-%2uT%2u:%2u:%2u",
        &year,
        &month,
        &day,
        &hour,
        &minute,
        &second
    );

    if (parsed != 6)
    {
        return false;
    }

    if (
        year < MIN_VALID_RTC_YEAR ||
        year > MAX_VALID_RTC_YEAR ||
        month < 1 ||
        month > 12 ||
        day < 1 ||
        day > daysInMonth(year, month) ||
        hour > 23 ||
        minute > 59 ||
        second > 59
    )
    {
        return false;
    }

    unixTime = DateTime(
        year,
        month,
        day,
        hour,
        minute,
        second
    ).unixtime();

    return true;
}

bool parseGraphCsvRecord(
    char *line,
    GraphSample &sample,
    bool &isAutoRecord,
    bool &isManualRecord,
    bool &hasTimestamp
)
{
    isAutoRecord = false;
    isManualRecord = false;
    hasTimestamp = false;

    char *fields[12];

    const size_t fieldCount =
        splitCsvFields(
            line,
            fields,
            12
        );

    if (fieldCount < 8)
    {
        return false;
    }

    hasTimestamp = parseIsoTimestamp(
        fields[1],
        sample.unixTime
    );

    isAutoRecord =
        strcmp(fields[2], "AUTO") == 0;

    isManualRecord =
        strcmp(fields[2], "MANUAL") == 0;

    if (!isAutoRecord)
    {
        return true;
    }

    char *endPointer = nullptr;

    sample.temperatureC = strtof(
        fields[5],
        &endPointer
    );

    if (
        endPointer == fields[5] ||
        !isfinite(sample.temperatureC)
    )
    {
        return false;
    }

    sample.humidityPercent = strtof(
        fields[6],
        &endPointer
    );

    if (
        endPointer == fields[6] ||
        !isfinite(sample.humidityPercent)
    )
    {
        return false;
    }

    sample.pressureHpa = strtof(
        fields[7],
        &endPointer
    );

    if (
        endPointer == fields[7] ||
        !isfinite(sample.pressureHpa)
    )
    {
        return false;
    }

    return hasTimestamp;
}

void calculateDisplayedGraphStatistics()
{
    resetGraphStatistics(
        graphDisplayTemperatureStats
    );

    resetGraphStatistics(
        graphDisplayHumidityStats
    );

    resetGraphStatistics(
        graphDisplayPressureStats
    );

    for (
        size_t index = 0;
        index < graphPointCount;
        index++
    )
    {
        addSampleToStatistics(
            graphSamples[index],
            graphDisplayTemperatureStats,
            graphDisplayHumidityStats,
            graphDisplayPressureStats
        );
    }
}

const char *currentGraphFilePath()
{
    if (graphViewingArchive)
    {
        return archiveDetailData.filePath;
    }

    return sessionFilePath;
}

const char *currentGraphStation()
{
    if (graphViewingArchive)
    {
        return archiveDetailData.station;
    }

    return station;
}

const char *currentGraphSessionId()
{
    if (graphViewingArchive)
    {
        return archiveDetailData.sessionId;
    }

    return sessionId;
}


bool scanGraphSessionFile(
    GraphRange requestedRange
)
{
    graphPointCount = 0;
    graphTotalAutoRecords = 0;
    graphTotalManualRecords = 0;
    graphSessionStartUnix = 0;
    graphSessionLastUnix = 0;
    graphDataReady = false;
    graphErrorMessage[0] = '\0';

    resetAllGraphStatistics();

    const char *sourceSessionId =
        currentGraphSessionId();

    if (
        sourceSessionId == nullptr ||
        sourceSessionId[0] == '\0' ||
        (
            !graphViewingArchive &&
            !sessionActive
        )
    )
    {
        snprintf(
            graphErrorMessage,
            sizeof(graphErrorMessage),
            "NIE JE VYBRANA RELACIA"
        );

        return false;
    }

    if (!ensureSDReady(false))
    {
        snprintf(
            graphErrorMessage,
            sizeof(graphErrorMessage),
            "SD KARTA NIE JE DOSTUPNA"
        );

        return false;
    }

    uint16_t partIndices[
        SESSION_MAX_FILE_PARTS
    ];

    const size_t partCount =
        collectSessionPartPaths(
            sourceSessionId,
            sharedSessionPartPaths,
            partIndices,
            SESSION_MAX_FILE_PARTS
        );

    if (partCount == 0)
    {
        snprintf(
            graphErrorMessage,
            sizeof(graphErrorMessage),
            "CSV CASTI RELACIE SA NENASLI"
        );

        return false;
    }

    char line[GRAPH_CSV_LINE_LENGTH];
    size_t recentCount = 0;
    size_t recentWriteIndex = 0;

    for (
        size_t part = 0;
        part < partCount;
        part++
    )
    {
        File file = SD.open(
            sharedSessionPartPaths[part],
            FILE_READ
        );

        if (!file)
        {
            snprintf(
                graphErrorMessage,
                sizeof(graphErrorMessage),
                "CSV CAST SA NEDA OTVORIT"
            );

            return false;
        }

        while (
            readCsvLine(
                file,
                line,
                sizeof(line)
            )
        )
        {
            GraphSample sample{};
            bool isAutoRecord = false;
            bool isManualRecord = false;
            bool hasTimestamp = false;

            const bool parsed =
                parseGraphCsvRecord(
                    line,
                    sample,
                    isAutoRecord,
                    isManualRecord,
                    hasTimestamp
                );

            if (
                hasTimestamp &&
                graphSessionStartUnix == 0
            )
            {
                graphSessionStartUnix =
                    sample.unixTime;
            }

            if (hasTimestamp)
            {
                graphSessionLastUnix =
                    sample.unixTime;
            }

            if (isManualRecord)
            {
                graphTotalManualRecords++;
            }

            if (
                !parsed ||
                !isAutoRecord
            )
            {
                continue;
            }

            graphTotalAutoRecords++;

            addSampleToStatistics(
                sample,
                graphTotalTemperatureStats,
                graphTotalHumidityStats,
                graphTotalPressureStats
            );

            if (
                requestedRange ==
                GraphRange::Last120
            )
            {
                graphRecentBuffer[
                    recentWriteIndex
                ] = sample;

                recentWriteIndex =
                    (
                        recentWriteIndex + 1
                    ) %
                    GRAPH_LAST_RECORD_COUNT;

                if (
                    recentCount <
                    GRAPH_LAST_RECORD_COUNT
                )
                {
                    recentCount++;
                }
            }
        }

        file.close();
    }

    if (graphTotalAutoRecords == 0)
    {
        snprintf(
            graphErrorMessage,
            sizeof(graphErrorMessage),
            "RELACIA ESTE NEMA AUTO DATA"
        );

        return false;
    }

    if (
        requestedRange ==
        GraphRange::Last120
    )
    {
        graphPointCount = recentCount;

        const size_t oldestIndex =
            recentCount <
            GRAPH_LAST_RECORD_COUNT
                ? 0
                : recentWriteIndex;

        for (
            size_t index = 0;
            index < recentCount;
            index++
        )
        {
            graphSamples[index] =
                graphRecentBuffer[
                    (
                        oldestIndex + index
                    ) %
                    GRAPH_LAST_RECORD_COUNT
                ];
        }

        calculateDisplayedGraphStatistics();
        graphDataReady = graphPointCount > 0;

        return graphDataReady;
    }

    // Druhy prechod cez vsetky casti relacie. Data sa
    // priebezne priemeruju do najviac 240 bodov.
    const uint32_t bucketSize =
        (
            graphTotalAutoRecords +
            GRAPH_MAX_POINT_COUNT -
            1
        ) /
        GRAPH_MAX_POINT_COUNT;

    uint32_t bucketCount = 0;
    double temperatureSum = 0.0;
    double humiditySum = 0.0;
    double pressureSum = 0.0;
    uint32_t bucketUnixTime = 0;

    for (
        size_t part = 0;
        part < partCount;
        part++
    )
    {
        File file = SD.open(
            sharedSessionPartPaths[part],
            FILE_READ
        );

        if (!file)
        {
            snprintf(
                graphErrorMessage,
                sizeof(graphErrorMessage),
                "CSV CAST SA NEDA OTVORIT"
            );

            return false;
        }

        while (
            readCsvLine(
                file,
                line,
                sizeof(line)
            )
        )
        {
            GraphSample sample{};
            bool isAutoRecord = false;
            bool isManualRecord = false;
            bool hasTimestamp = false;

            if (
                !parseGraphCsvRecord(
                    line,
                    sample,
                    isAutoRecord,
                    isManualRecord,
                    hasTimestamp
                ) ||
                !isAutoRecord
            )
            {
                continue;
            }

            if (bucketCount == 0)
            {
                bucketUnixTime =
                    sample.unixTime;
            }

            temperatureSum +=
                sample.temperatureC;

            humiditySum +=
                sample.humidityPercent;

            pressureSum +=
                sample.pressureHpa;

            bucketCount++;

            if (
                bucketCount >= bucketSize &&
                graphPointCount <
                GRAPH_MAX_POINT_COUNT
            )
            {
                graphSamples[
                    graphPointCount++
                ] = GraphSample{
                    bucketUnixTime,
                    static_cast<float>(
                        temperatureSum /
                        bucketCount
                    ),
                    static_cast<float>(
                        humiditySum /
                        bucketCount
                    ),
                    static_cast<float>(
                        pressureSum /
                        bucketCount
                    )
                };

                bucketCount = 0;
                temperatureSum = 0.0;
                humiditySum = 0.0;
                pressureSum = 0.0;
            }
        }

        file.close();
    }

    if (
        bucketCount > 0 &&
        graphPointCount <
        GRAPH_MAX_POINT_COUNT
    )
    {
        graphSamples[
            graphPointCount++
        ] = GraphSample{
            bucketUnixTime,
            static_cast<float>(
                temperatureSum /
                bucketCount
            ),
            static_cast<float>(
                humiditySum /
                bucketCount
            ),
            static_cast<float>(
                pressureSum /
                bucketCount
            )
        };
    }

    graphDisplayTemperatureStats =
        graphTotalTemperatureStats;

    graphDisplayHumidityStats =
        graphTotalHumidityStats;

    graphDisplayPressureStats =
        graphTotalPressureStats;

    graphDataReady = graphPointCount > 0;

    return graphDataReady;
}

// ============================================================
// GRAFY - PRIEBEZNA AKTUALIZACIA
// ============================================================

GraphSample graphSampleFromMeasurement(
    const Measurement &measurement
)
{
    return GraphSample{
        measurement.timestamp.unixtime(),
        measurement.temperatureC,
        measurement.humidityPercent,
        measurement.pressureHpa
    };
}

void appendGraphSampleToLast120(
    const GraphSample &sample
)
{
    if (
        graphPointCount <
        GRAPH_LAST_RECORD_COUNT
    )
    {
        graphSamples[
            graphPointCount++
        ] = sample;
    }
    else
    {
        for (
            size_t index = 1;
            index < GRAPH_LAST_RECORD_COUNT;
            index++
        )
        {
            graphSamples[
                index - 1
            ] = graphSamples[index];
        }

        graphSamples[
            GRAPH_LAST_RECORD_COUNT - 1
        ] = sample;

        graphPointCount =
            GRAPH_LAST_RECORD_COUNT;
    }

    calculateDisplayedGraphStatistics();
    graphDataReady = graphPointCount > 0;
}

void registerSuccessfulAutoRecordForGraph(
    const Measurement &measurement
)
{
    if (
        currentScreen != Screen::Graphs ||
        graphViewingArchive ||
        !measurement.valid
    )
    {
        return;
    }

    const GraphSample sample =
        graphSampleFromMeasurement(
            measurement
        );

    graphTotalAutoRecords++;

    if (graphSessionStartUnix == 0)
    {
        graphSessionStartUnix =
            sample.unixTime;
    }

    graphSessionLastUnix =
        sample.unixTime;

    addSampleToStatistics(
        sample,
        graphTotalTemperatureStats,
        graphTotalHumidityStats,
        graphTotalPressureStats
    );

    graphErrorMessage[0] = '\0';

    if (
        graphRange ==
        GraphRange::Last120
    )
    {
        appendGraphSampleToLast120(
            sample
        );

        drawGraphSummary(false);
        drawGraphPlot();

        lastGraphDataRefreshMillis =
            millis();

        lastGraphSummaryRefreshMillis =
            lastGraphDataRefreshMillis;

        return;
    }

    // Kym ma cela relacia najviac 240 AUTO zaznamov,
    // je mozne novy bod pridat priamo bez citania CSV.
    if (
        graphTotalAutoRecords <=
            GRAPH_MAX_POINT_COUNT &&
        graphPointCount <
            GRAPH_MAX_POINT_COUNT
    )
    {
        graphSamples[
            graphPointCount++
        ] = sample;

        graphDisplayTemperatureStats =
            graphTotalTemperatureStats;

        graphDisplayHumidityStats =
            graphTotalHumidityStats;

        graphDisplayPressureStats =
            graphTotalPressureStats;

        graphDataReady = true;

        drawGraphSummary(false);
        drawGraphPlot();

        lastGraphDataRefreshMillis =
            millis();

        lastGraphSummaryRefreshMillis =
            lastGraphDataRefreshMillis;

        return;
    }

    // Pri vacsej relacii je graf VSETKY zmenseny do intervalov.
    // Po novom zapise preto oznacime data na bezpecne obnovenie.
    graphDisplayTemperatureStats =
        graphTotalTemperatureStats;

    graphDisplayHumidityStats =
        graphTotalHumidityStats;

    graphDisplayPressureStats =
        graphTotalPressureStats;

    graphFullRangeRefreshPending = true;

    // Pocitadlo a trvanie relacie sa aktualizuju okamzite.
    drawGraphSummary(false);
    lastGraphSummaryRefreshMillis =
        millis();
}

void updateLiveGraphScreen(
    uint32_t currentMillis
)
{
    if (
        currentScreen != Screen::Graphs ||
        graphViewingArchive
    )
    {
        return;
    }

    if (
        currentMillis -
            lastGraphSummaryRefreshMillis >=
        GRAPH_SUMMARY_REFRESH_INTERVAL_MS
    )
    {
        lastGraphSummaryRefreshMillis =
            currentMillis;

        drawGraphSummary(false);
    }

    if (
        graphRange != GraphRange::All ||
        !graphFullRangeRefreshPending
    )
    {
        return;
    }

    if (
        currentMillis -
            lastGraphDataRefreshMillis <
        GRAPH_ALL_REFRESH_MIN_INTERVAL_MS
    )
    {
        return;
    }

    scanGraphSessionFile(
        GraphRange::All
    );

    graphFullRangeRefreshPending = false;
    lastGraphDataRefreshMillis =
        currentMillis;
    lastGraphSummaryRefreshMillis =
        currentMillis;

    drawGraphSummary(false);
    drawGraphPlot();
}

float graphSampleValue(
    const GraphSample &sample,
    GraphParameter parameter
)
{
    switch (parameter)
    {
        case GraphParameter::Humidity:
            return sample.humidityPercent;

        case GraphParameter::Pressure:
            return sample.pressureHpa;

        case GraphParameter::Temperature:
        default:
            return sample.temperatureC;
    }
}

const GraphStatistics &selectedGraphStatistics()
{
    switch (graphParameter)
    {
        case GraphParameter::Humidity:
            return graphDisplayHumidityStats;

        case GraphParameter::Pressure:
            return graphDisplayPressureStats;

        case GraphParameter::Temperature:
        default:
            return graphDisplayTemperatureStats;
    }
}

const char *graphParameterTitle()
{
    switch (graphParameter)
    {
        case GraphParameter::Humidity:
            return "VLHKOST (%)";

        case GraphParameter::Pressure:
            return "TLAK (hPa)";

        case GraphParameter::Temperature:
        default:
            return "TEPLOTA (C)";
    }
}

uint16_t graphLineColor()
{
    switch (graphParameter)
    {
        case GraphParameter::Humidity:
            return TFT_CYAN;

        case GraphParameter::Pressure:
            return COLOR_OK;

        case GraphParameter::Temperature:
        default:
            return COLOR_PRIMARY;
    }
}

void formatGraphDuration(
    uint32_t durationSeconds,
    char *buffer,
    size_t bufferSize
)
{
    const uint32_t hours =
        durationSeconds / 3600UL;

    const uint32_t minutes =
        (
            durationSeconds % 3600UL
        ) /
        60UL;

    const uint32_t seconds =
        durationSeconds % 60UL;

    if (hours > 99)
    {
        snprintf(
            buffer,
            bufferSize,
            "%luh %02lum",
            static_cast<unsigned long>(hours),
            static_cast<unsigned long>(minutes)
        );
    }
    else
    {
        snprintf(
            buffer,
            bufferSize,
            "%02lu:%02lu:%02lu",
            static_cast<unsigned long>(hours),
            static_cast<unsigned long>(minutes),
            static_cast<unsigned long>(seconds)
        );
    }
}

void formatGraphTime(
    uint32_t unixTime,
    char *buffer,
    size_t bufferSize
)
{
    if (unixTime == 0)
    {
        snprintf(
            buffer,
            bufferSize,
            "--:--"
        );

        return;
    }

    const DateTime time(unixTime);

    snprintf(
        buffer,
        bufferSize,
        "%02u:%02u",
        time.hour(),
        time.minute()
    );
}

void drawGraphLoadingScreen()
{
    currentScreen = Screen::Graphs;

    tft.fillScreen(COLOR_BACKGROUND);
    tft.fillRect(0, 0, 320, 40, COLOR_PANEL);
    tft.drawFastHLine(
        0,
        39,
        320,
        COLOR_PANEL_BORDER
    );

    tft.setTextDatum(MC_DATUM);
    tft.setTextColor(COLOR_TEXT, COLOR_PANEL);
    tft.drawString(
        "GRAFY RELACIE",
        160,
        20,
        2
    );

    tft.setTextColor(
        COLOR_PRIMARY,
        COLOR_BACKGROUND
    );

    tft.drawString(
        "NACITAVAM CSV...",
        160,
        230,
        2
    );
}
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
void loop()
{
    processTouch();
    updateTimedUiEvents();

    const uint32_t currentMillis = millis();

    if (
        currentScreen == Screen::Recovery &&
        !sdReady
    )
    {
        const bool recovered =
            ensureSDReady(false);

        if (recovered)
        {
            drawRecoveryScreen();
        }
    }

    if (
        currentMillis - lastBatteryMillis >=
        BATTERY_INTERVAL_MS
    )
    {
        lastBatteryMillis = currentMillis;
        readBatteryState();
        updateBatteryWarning();

        if (currentScreen == Screen::Main)
        {
            updateDateTimeDisplay(
                currentMeasurement.timestamp
            );

            updateMessageStrip();
        }
    }

    // Senzory sa citaju aj pocas otvorenej klavesnice.
    if (
        currentMillis - lastSensorMillis >=
        SENSOR_INTERVAL_MS
    )
    {
        lastSensorMillis = currentMillis;

        currentMeasurement = readMeasurement();
        printMeasurement(currentMeasurement);

        if (currentScreen == Screen::Main)
        {
            updateMainScreen();
        }
        else if (currentScreen == Screen::Calibration)
        {
            drawCalibrationLivePanel(false);
        }
    }

    // Automaticky zapis bezi iba po zadani stanoviska
    // a vytvoreni meracej relacie.
    if (
        sessionActive &&
        currentMillis - lastAutoLogMillis >=
        static_cast<uint32_t>(autoLogIntervalSeconds) * 1000UL
    )
    {
        lastAutoLogMillis = currentMillis;

        if (!currentMeasurement.valid)
        {
            lastAutoWriteOk = false;

            setStatusMessage(
                measurementErrorText(
                    lastMeasurementError
                ),
                COLOR_ERROR,
                4000
            );
        }
        else
        {
            lastAutoWriteOk =
                appendMeasurementToSession(
                    currentMeasurement,
                    "AUTO",
                    station,
                    ""
                );

            if (lastAutoWriteOk)
            {
                registerSuccessfulAutoRecordForGraph(
                    currentMeasurement
                );
            }

            if (!lastAutoWriteOk)
            {
                persistActiveSessionState();

                setStatusMessage(
                    sdWriteBlockedBySpace
                        ? "SD KARTA JE PLNA - AUTOMATICKY ZAPIS ZASTAVENY"
                        : "CHYBA AUTOMATICKEHO ZAPISU - KONTROLA SD",
                    COLOR_ERROR,
                    5000
                );
            }
        }

        if (currentScreen == Screen::Main)
        {
            updateStatusPanel();
            updateMessageStrip();
        }
    }

    if (sdReady)
    {
        refreshSdSpaceInfo(false);
    }

    updateLiveGraphScreen(
        currentMillis
    );

    updateWifiExport(
        currentMillis
    );

    updateDisplayPowerSaving(
        currentMillis
    );
}
